brucejcooper/light_controller/kicad/programmer/programmer.kicad_pcb

## KiCad design cores/cps3/sch/buffer_line_driver.kicad_sch

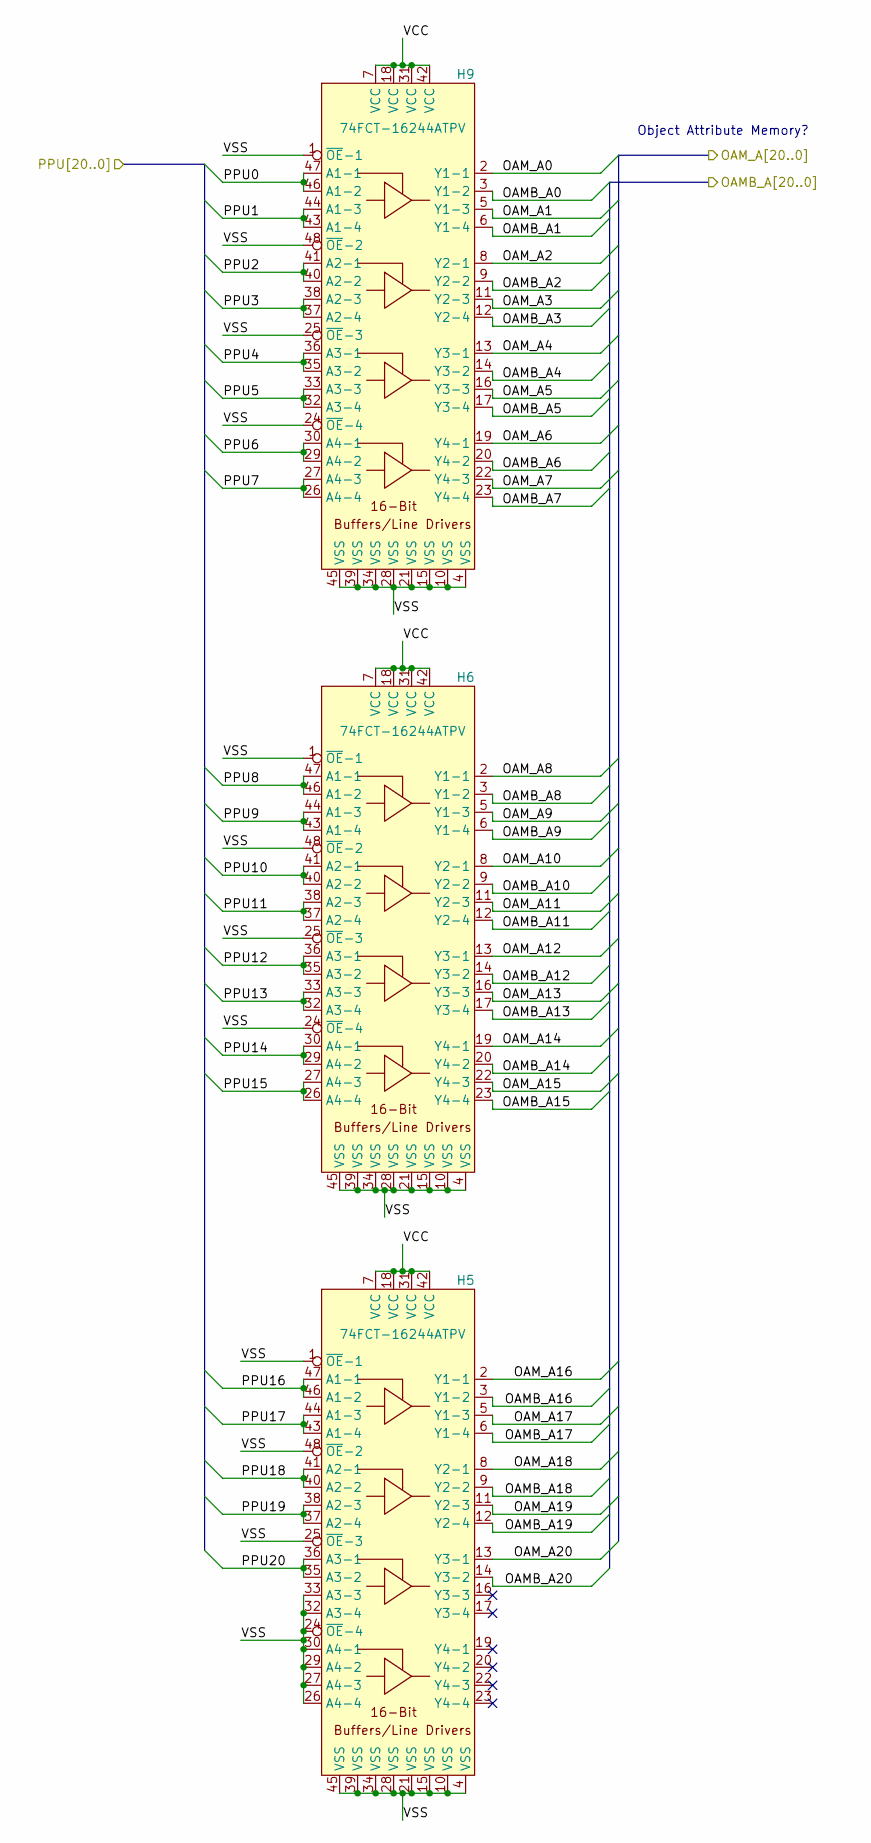
[picture p15: schematic buffer_line_driver.kicad_sch]

Parts:
H5, H6, H9: 74FCT-16244ATPV

Connections:
OAMB_A0: H9.3 (Y1-2)
OAMB_A1: H9.6 (Y1-4)
OAMB_A2: H9.9 (Y2-2)
OAMB_A3: H9.12 (Y2-4)
OAMB_A4: H9.14 (Y3-2)
OAMB_A5: H9.17 (Y3-4)
OAMB_A6: H9.20 (Y4-2)
OAMB_A7: H9.23 (Y4-4)
OAMB_A8: H6.3 (Y1-2)
OAMB_A9: H6.6 (Y1-4)
OAMB_A10: H6.9 (Y2-2)
OAMB_A11: H6.12 (Y2-4)
OAMB_A12: H6.14 (Y3-2)
OAMB_A13: H6.17 (Y3-4)
OAMB_A14: H6.20 (Y4-2)
OAMB_A15: H6.23 (Y4-4)
OAMB_A16: H5.3 (Y1-2)
OAMB_A17: H5.6 (Y1-4)
OAMB_A18: H5.9 (Y2-2)
OAMB_A19: H5.12 (Y2-4)
OAMB_A20: H5.14 (Y3-2)
OAM_A0: H9.2 (Y1-1)
OAM_A1: H9.5 (Y1-3)
OAM_A2: H9.8 (Y2-1)
OAM_A3: H9.11 (Y2-3)
OAM_A4: H9.13 (Y3-1)
OAM_A5: H9.16 (Y3-3)
OAM_A6: H9.19 (Y4-1)
OAM_A7: H9.22 (Y4-3)
OAM_A8: H6.2 (Y1-1)
OAM_A9: H6.5 (Y1-3)
OAM_A10: H6.8 (Y2-1)
OAM_A11: H6.11 (Y2-3)
OAM_A12: H6.13 (Y3-1)
OAM_A13: H6.16 (Y3-3)
OAM_A14: H6.19 (Y4-1)
OAM_A15: H6.22 (Y4-3)
OAM_A16: H5.2 (Y1-1)
OAM_A17: H5.5 (Y1-3)
OAM_A18: H5.8 (Y2-1)
OAM_A19: H5.11 (Y2-3)
OAM_A20: H5.13 (Y3-1)
PPU0: H9.46 (A1-2), H9.47 (A1-1)
PPU1: H9.43 (A1-4), H9.44 (A1-3)
PPU2: H9.40 (A2-2), H9.41 (A2-1)
PPU3: H9.37 (A2-4), H9.38 (A2-3)
PPU4: H9.35 (A3-2), H9.36 (A3-1)
PPU5: H9.32 (A3-4), H9.33 (A3-3)
PPU6: H9.29 (A4-2), H9.30 (A4-1)
PPU7: H9.26 (A4-4), H9.27 (A4-3)
PPU8: H6.46 (A1-2), H6.47 (A1-1)
PPU9: H6.43 (A1-4), H6.44 (A1-3)
PPU10: H6.40 (A2-2), H6.41 (A2-1)
PPU11: H6.37 (A2-4), H6.38 (A2-3)
PPU12: H6.35 (A3-2), H6.36 (A3-1)
PPU13: H6.32 (A3-4), H6.33 (A3-3)
PPU14: H6.29 (A4-2), H6.30 (A4-1)
PPU15: H6.26 (A4-4), H6.27 (A4-3)
PPU16: H5.46 (A1-2), H5.47 (A1-1)
PPU17: H5.43 (A1-4), H5.44 (A1-3)
PPU18: H5.40 (A2-2), H5.41 (A2-1)
PPU19: H5.37 (A2-4), H5.38 (A2-3)
PPU20: H5.35 (A3-2), H5.36 (A3-1)
VCC: H5.7 (VCC), H5.18 (VCC), H5.31 (VCC), H5.42 (VCC), H6.7 (VCC), H6.18 (VCC), H6.31 (VCC), H6.42 (VCC), H9.7 (VCC), H9.18 (VCC), H9.31 (VCC), H9.42 (VCC)
VSS: H5.1 (~OE-1), H5.4 (VSS), H5.10 (VSS), H5.15 (VSS), H5.21 (VSS), H5.24 (~OE-4), H5.25 (~OE-3), H5.26 (A4-4), H5.27 (A4-3), H5.28 (VSS), H5.29 (A4-2), H5.30 (A4-1), H5.32 (A3-4), H5.33 (A3-3), H5.34 (VSS), H5.39 (VSS), H5.45 (VSS), H5.48 (~OE-2), H6.1 (~OE-1), H6.4 (VSS), H6.10 (VSS), H6.15 (VSS), H6.21 (VSS), H6.24 (~OE-4), H6.25 (~OE-3), H6.28 (VSS), H6.34 (VSS), H6.39 (VSS), H6.45 (VSS), H6.48 (~OE-2), H9.1 (~OE-1), H9.4 (VSS), H9.10 (VSS), H9.15 (VSS), H9.21 (VSS), H9.24 (~OE-4), H9.25 (~OE-3), H9.28 (VSS), H9.34 (VSS), H9.39 (VSS), H9.45 (VSS), H9.48 (~OE-2)

Notes on the sheet:
Object Attribute Memory?
