brucejcooper/light_controller/kicad/programmer/programmer.kicad_pcb

## KiCad design cores/cps3/sch/cassette.kicad_sch

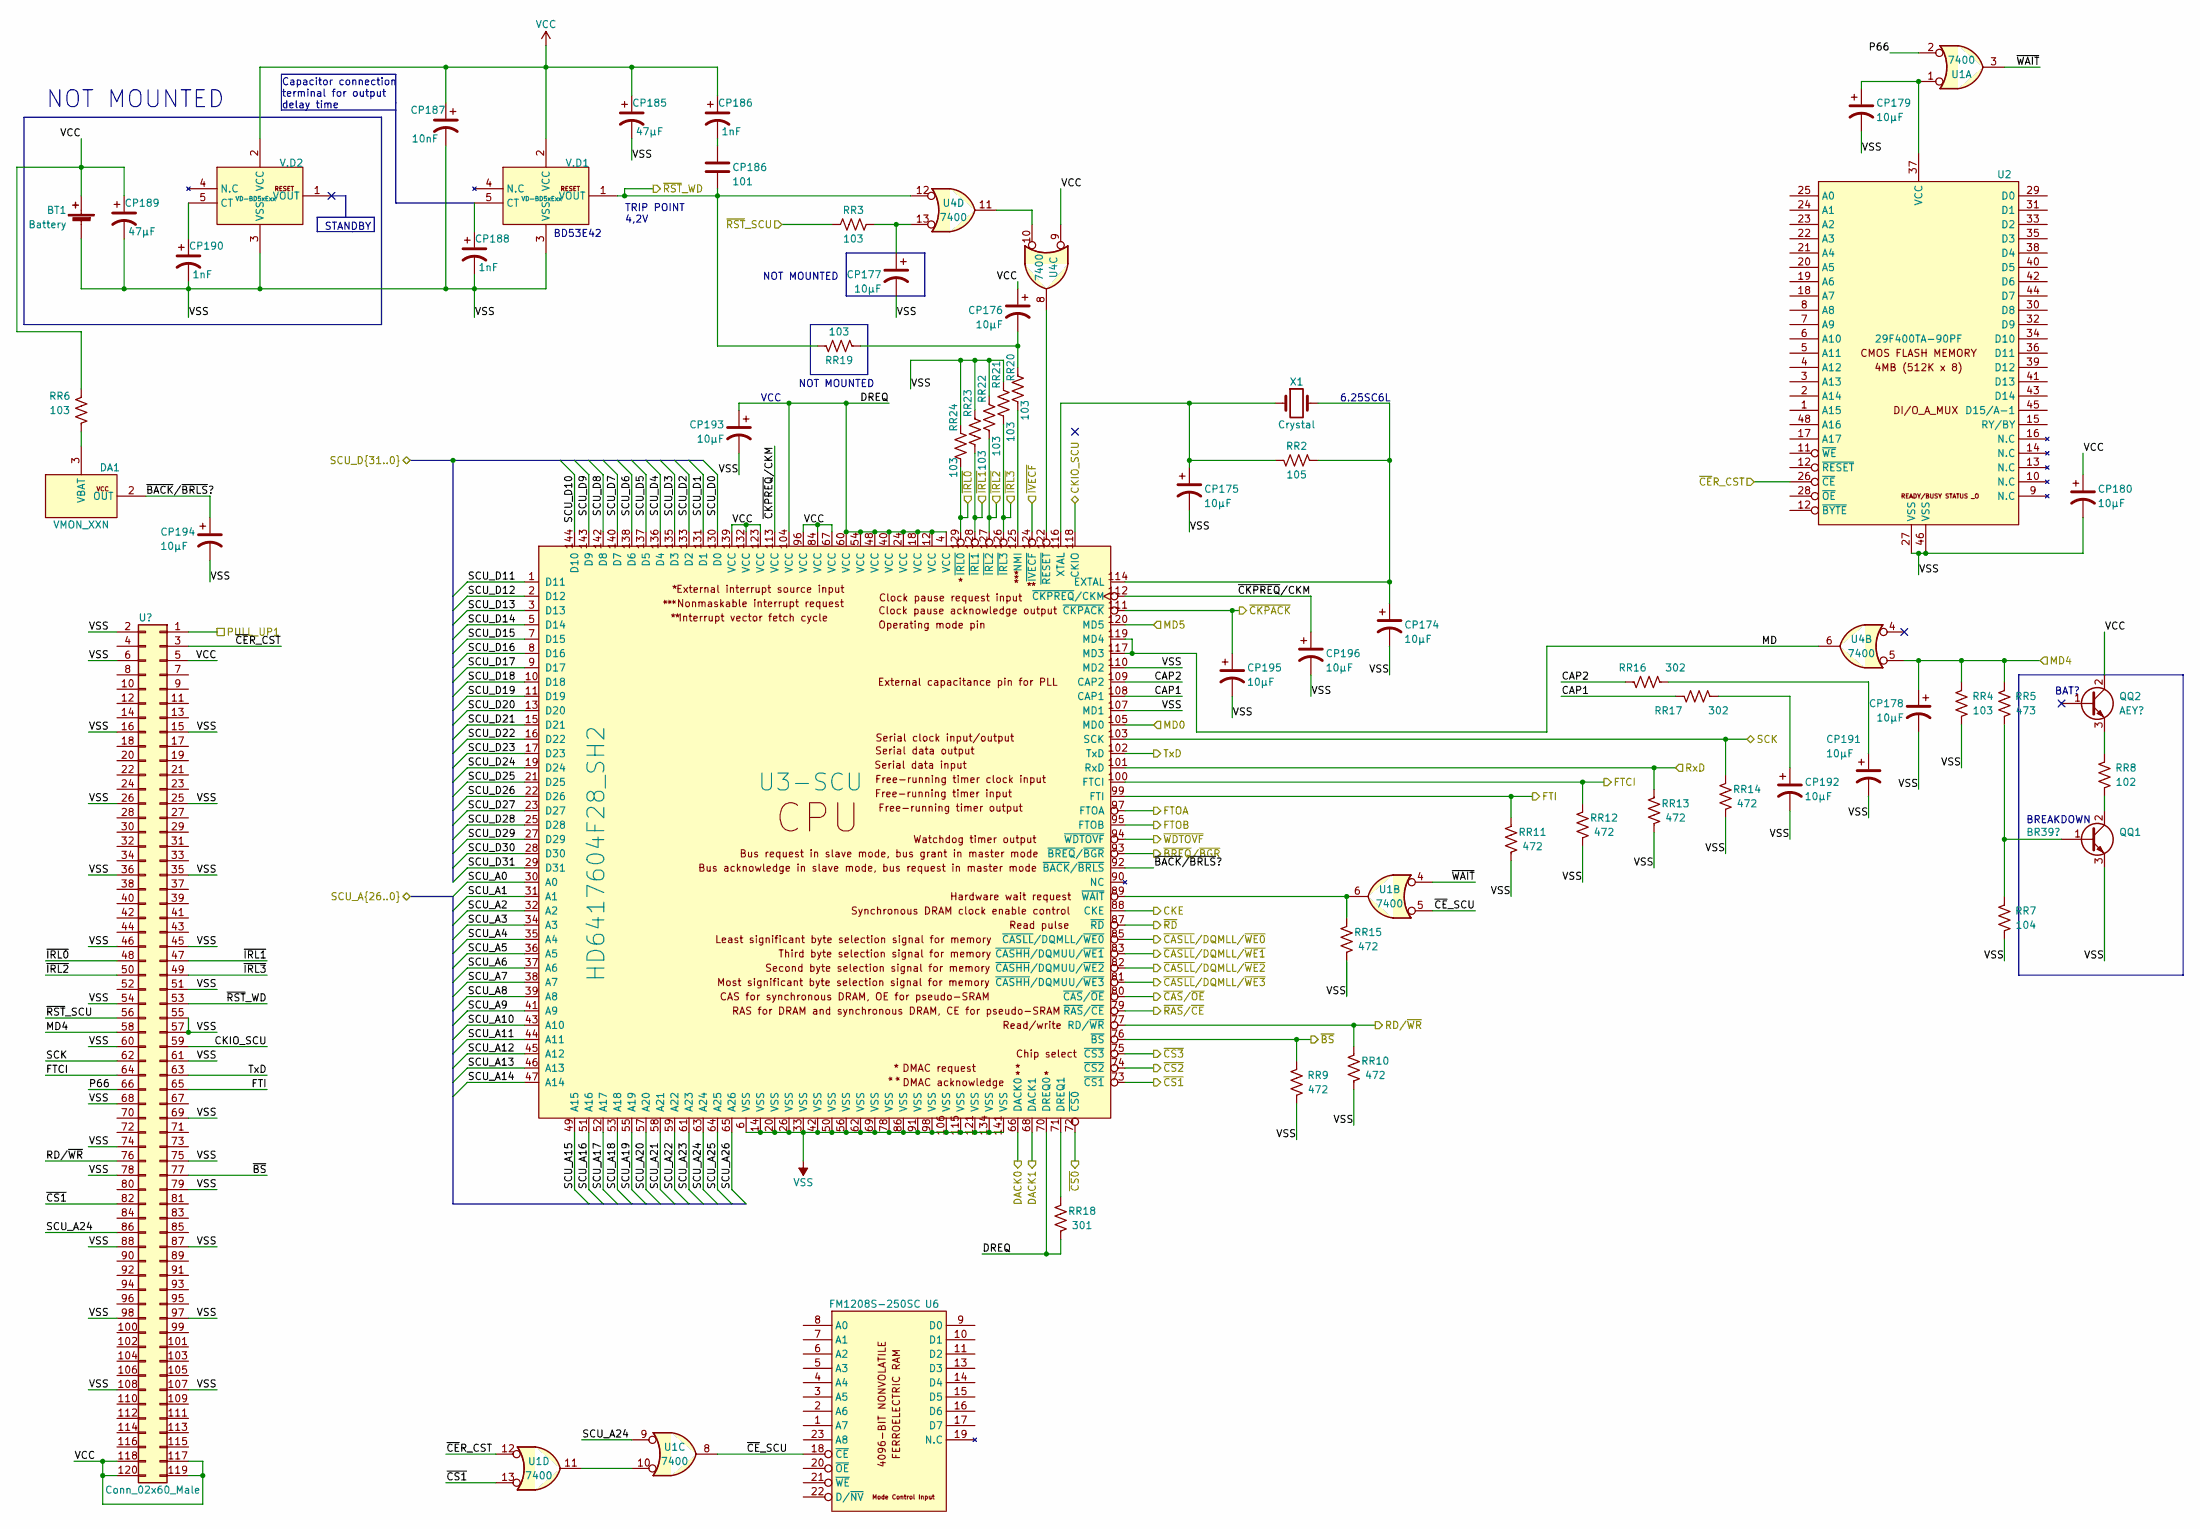
[picture p17: schematic cassette.kicad_sch]

Parts:
BT1: Battery
CP174, CP175, CP176, CP177, CP178, CP179, CP180, CP191, CP192, CP193, CP194, CP195, CP196: 10μF
CP185, CP189: 47μF
CP186: 101
CP187: 10nF
CP188, CP190: 1nF
DA1: VMON_XXN
QQ1: BR39?
QQ2: AEY?
RR2: 105
RR3, RR4, RR6, RR19, RR20, RR21, RR22, RR23, RR24: 103
RR5: 473
RR7: 104
RR8: 102
RR9, RR10, RR11, RR12, RR13, RR14, RR15: 472
RR16, RR17: 302
RR18: 301
U1, U4: 7400
U2: 29F400TA-90PF
U3-SCU: HD6417604F28_SH2
U6: FM1208S-250SC
V.D1, V.D2: VD-BD5xExx
X1: Crystal

Connections:
CAP1: RR17.2, U3-SCU.108 (CAP1)
CAP2: RR16.2, U3-SCU.109 (CAP2)
CKE: U3-SCU.88 (CKE)
CKIO_SCU: U3-SCU.118 (CKIO)
DACK0: U3-SCU.66 (DACK0)
DACK1: U3-SCU.68 (DACK1)
DREQ: CP193.1, RR18.2, U3-SCU.4 (VCC), U3-SCU.12 (VCC), U3-SCU.18 (VCC), U3-SCU.24 (VCC), U3-SCU.40 (VCC), U3-SCU.48 (VCC), U3-SCU.54 (VCC), U3-SCU.60 (VCC), U3-SCU.70 (DREQ0), U3-SCU.104 (VCC)
FTCI: RR12.2, U3-SCU.100 (FTCI)
FTI: RR11.2, U3-SCU.99 (FTI)
FTOA: U3-SCU.97 (FTOA)
FTOB: U3-SCU.95 (FTOB)
MD: U3-SCU.117 (MD3), U3-SCU.119 (MD4), U4.6
MD0: U3-SCU.105 (MD0)
MD4: CP178.1, RR4.2, RR5.2, U4.5
MD5: U3-SCU.120 (MD5)
unnamed: CP174.1, RR2.2, U3-SCU.114 (EXTAL), X1.2
unnamed: CP175.1, RR2.1, U3-SCU.116 (XTAL), X1.1
unnamed: CP176.2, RR19.2, RR20.2
unnamed: CP177.1, RR3.2, U4.13
unnamed: CP179.1, U1.1, U2.37 (VCC)
unnamed: CP185.1, CP186.1, CP187.1, V.D1.2 (VCC), V.D2.2 (VCC)
unnamed: CP188.1, V.D1.5 (CT)
unnamed: CP190.1, V.D2.5 (CT)
unnamed: CP191.1, RR16.1
unnamed: CP192.1, RR17.1
unnamed: DA1.3 (VBAT), RR6.1
unnamed: QQ1.1 (B), RR5.1, RR7.2
unnamed: QQ1.2 (C), RR8.1
unnamed: QQ2.3 (E), RR8.2
unnamed: RR15.2, U1.6, U3-SCU.89 (~WAIT)
unnamed: RR18.1, U3-SCU.71 (DREQ1)
unnamed: RR20.1, U3-SCU.125 (NMI)
unnamed: U1.10, U1.11
unnamed: U3-SCU.6 (VSS), U3-SCU.14 (VSS), U3-SCU.20 (VSS), U3-SCU.26 (VSS), U3-SCU.33 (VSS), U3-SCU.42 (VSS), U3-SCU.50 (VSS), U3-SCU.56 (VSS), U3-SCU.62 (VSS), U3-SCU.69 (VSS), U3-SCU.78 (VSS), U3-SCU.86 (VSS), U3-SCU.91 (VSS), U3-SCU.98 (VSS), U3-SCU.106 (VSS), U3-SCU.115 (VSS), U3-SCU.121 (VSS), U3-SCU.134 (VSS), U3-SCU.141 (VSS)
unnamed: U3-SCU.122 (~RESET), U4.8
unnamed: U4.10, U4.11
P66: U1.2
RD/~WR: RR10.2, U3-SCU.77 (RD/~WR)
RxD: RR13.2, U3-SCU.101 (RxD)
SCK: RR14.2, U3-SCU.103 (SCK)
SCU_A0: U3-SCU.30 (A0)
SCU_A1: U3-SCU.31 (A1)
SCU_A2: U3-SCU.32 (A2)
SCU_A3: U3-SCU.34 (A3)
SCU_A4: U3-SCU.35 (A4)
SCU_A5: U3-SCU.36 (A5)
SCU_A6: U3-SCU.37 (A6)
SCU_A7: U3-SCU.38 (A7)
SCU_A8: U3-SCU.39 (A8)
SCU_A9: U3-SCU.41 (A9)
SCU_A10: U3-SCU.43 (A10)
SCU_A11: U3-SCU.44 (A11)
SCU_A12: U3-SCU.45 (A12)
SCU_A13: U3-SCU.46 (A13)
SCU_A14: U3-SCU.47 (A14)
SCU_A15: U3-SCU.49 (A15)
SCU_A16: U3-SCU.51 (A16)
SCU_A17: U3-SCU.52 (A17)
SCU_A18: U3-SCU.53 (A18)
SCU_A19: U3-SCU.55 (A19)
SCU_A20: U3-SCU.57 (A20)
SCU_A21: U3-SCU.58 (A21)
SCU_A22: U3-SCU.59 (A22)
SCU_A23: U3-SCU.61 (A23)
SCU_A24: U1.9, U3-SCU.63 (A24)
SCU_A25: U3-SCU.64 (A25)
SCU_A26: U3-SCU.65 (A26)
SCU_D0: U3-SCU.130 (D0)
SCU_D1: U3-SCU.131 (D1)
SCU_D2: U3-SCU.133 (D2)
SCU_D3: U3-SCU.135 (D3)
SCU_D4: U3-SCU.136 (D4)
SCU_D5: U3-SCU.137 (D5)
SCU_D6: U3-SCU.138 (D6)
SCU_D7: U3-SCU.140 (D7)
SCU_D8: U3-SCU.142 (D8)
SCU_D9: U3-SCU.143 (D9)
SCU_D10: U3-SCU.144 (D10)
SCU_D11: U3-SCU.1 (D11)
SCU_D12: U3-SCU.2 (D12)
SCU_D13: U3-SCU.3 (D13)
SCU_D14: U3-SCU.5 (D14)
SCU_D15: U3-SCU.7 (D15)
SCU_D16: U3-SCU.8 (D16)
SCU_D17: U3-SCU.9 (D17)
SCU_D18: U3-SCU.10 (D18)
SCU_D19: U3-SCU.11 (D19)
SCU_D20: U3-SCU.13 (D20)
SCU_D21: U3-SCU.15 (D21)
SCU_D22: U3-SCU.16 (D22)
SCU_D23: U3-SCU.17 (D23)
SCU_D24: U3-SCU.19 (D24)
SCU_D25: U3-SCU.21 (D25)
SCU_D26: U3-SCU.22 (D26)
SCU_D27: U3-SCU.23 (D27)
SCU_D28: U3-SCU.25 (D28)
SCU_D29: U3-SCU.27 (D29)
SCU_D30: U3-SCU.28 (D30)
SCU_D31: U3-SCU.29 (D31)
TxD: U3-SCU.102 (TxD)
VCC: BT1.1 (+), CP176.1, CP180.1, CP189.1, QQ2.2 (C), RR6.2, U3-SCU.67 (VCC), U3-SCU.84 (VCC), U3-SCU.96 (VCC), U3-SCU.123 (VCC), U3-SCU.132 (VCC), U3-SCU.139 (VCC), U4.9
VSS: BT1.2 (-), CP174.2, CP175.2, CP177.2, CP178.2, CP179.2, CP180.2, CP185.2, CP187.2, CP188.2, CP189.2, CP190.2, CP191.2, CP192.2, CP193.2, CP194.2, CP195.2, CP196.2, QQ1.3 (E), RR4.1, RR7.1, RR9.1, RR10.1, RR11.1, RR12.1, RR13.1, RR14.1, RR15.1, RR21.2, RR22.2, RR23.2, RR24.2, U2.27 (VSS), U2.46 (VSS), U3-SCU.107 (MD1), U3-SCU.110 (MD2), V.D1.3 (VSS), V.D2.3 (VSS)
~BACK/~BRLS?: CP194.1, DA1.2 (OUT), U3-SCU.92 (~BACK/~BRLS)
~BREQ/~BGR: U3-SCU.93 (~BREQ/~BGR)
~BS: RR9.2, U3-SCU.76 (~BS)
~CASLL/DQMLL/~WE0: U3-SCU.85 (~CASLL/DQMLL/~WE0)
~CASLL/DQMLL/~WE1: U3-SCU.83 (~CASHH/DQMUU/~WE1)
~CASLL/DQMLL/~WE2: U3-SCU.82 (~CASHH/DQMUU/~WE2)
~CASLL/DQMLL/~WE3: U3-SCU.81 (~CASHH/DQMUU/~WE3)
~CAS/~OE: U3-SCU.80 (~CAS/~OE)
~CER_CST: U1.12, U2.26 (~CE)
~CE_SCU: U1.5, U1.8, U6.18 (~CE)
~CKPACK: CP195.1, U3-SCU.111 (~CKPACK)
~CKPREQ/CKM: CP196.1, U3-SCU.112 (~CKPREQ/CKM), U3-SCU.113 (VCC)
~CS0: U3-SCU.72 (~CS0)
~CS1: U1.13, U3-SCU.73 (~CS1)
~CS2: U3-SCU.74 (~CS2)
~CS3: U3-SCU.75 (~CS3)
~IRL0: RR24.1, U3-SCU.129 (~IRL0)
~IRL1: RR23.1, U3-SCU.128 (~IRL1)
~IRL2: RR22.1, U3-SCU.127 (~IRL2)
~IRL3: RR21.1, U3-SCU.126 (~IRL3)
~IVECF: U3-SCU.124 (~IVECF)
~RAS/~CE: U3-SCU.79 (~RAS/~CE)
~RD: U3-SCU.87 (~RD)
~RST_SCU: RR3.1
~RST_WD: CP186.1, RR19.1, U4.12, V.D1.1 (VOUT)
~WAIT: U1.3, U1.4
~WDTOVF: U3-SCU.94 (~WDTOVF)

Notes on the sheet:
BREAKDOWN
Capacitor connection terminal for output delay time
VCC
BAT?
6.25SC6L
BD53E42
NOT MOUNTED
TRIP POINT 4,2V
STANDBY
