brucejcooper/light_controller/kicad/programmer/programmer.kicad_pcb

## KiCad design cores/cps3/sch/memories_fb.kicad_sch

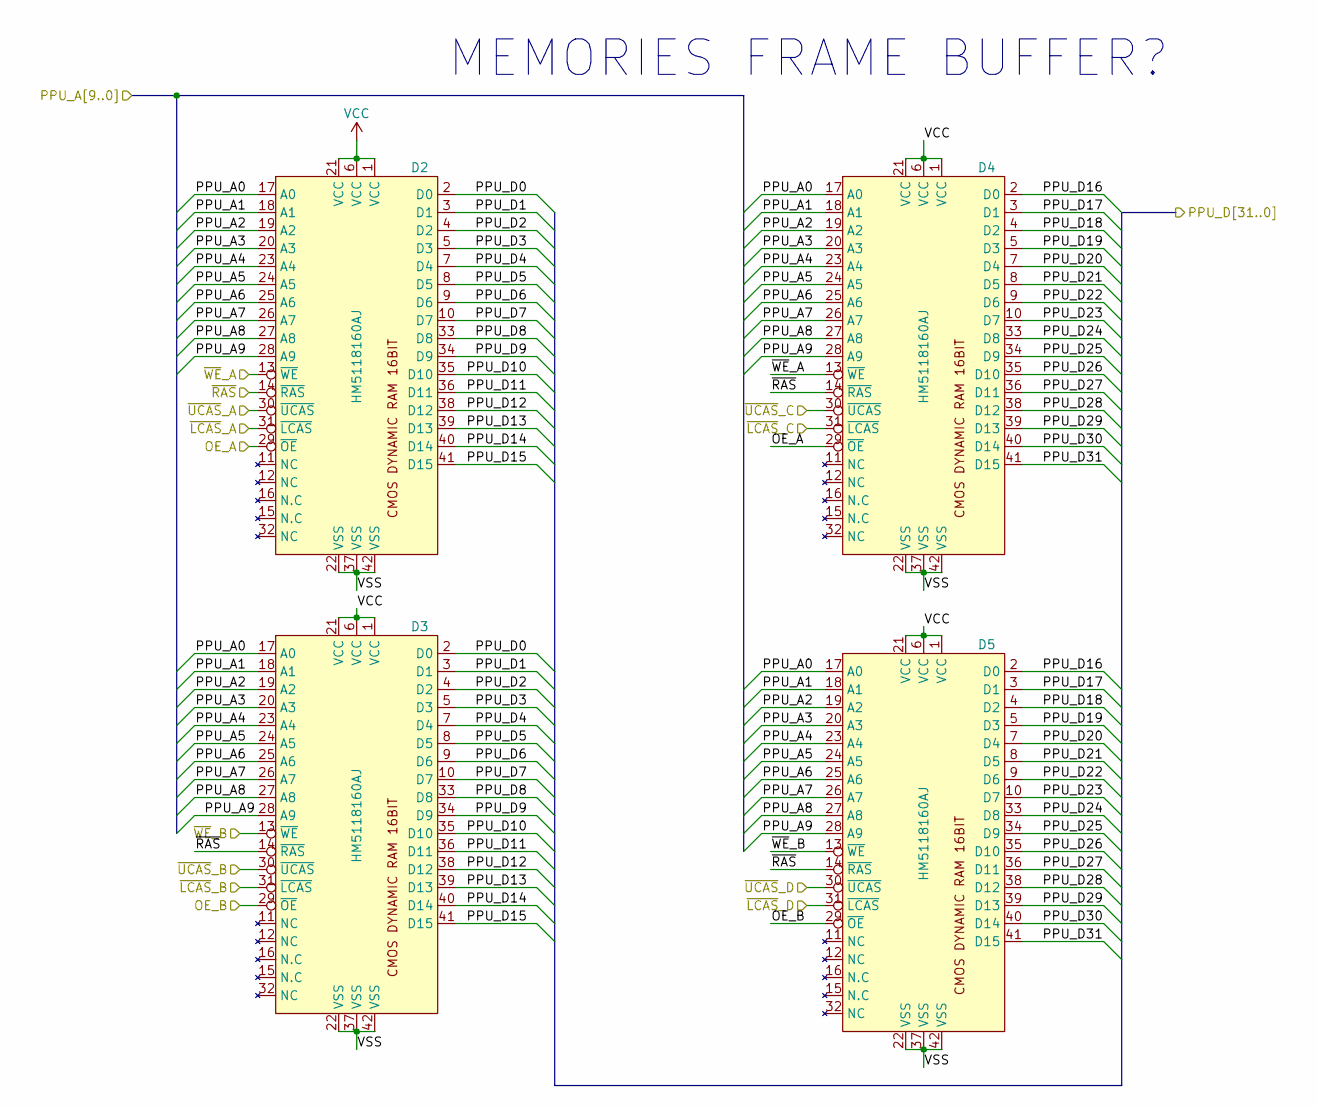
[picture p21: schematic memories_fb.kicad_sch]

Parts:
D2, D3, D4, D5: HM5118160AJ

Connections:
unnamed: D2.1 (VCC), D2.6 (VCC), D2.21 (VCC)
OE_A: D2.29 (~OE), D4.29 (~OE)
OE_B: D3.29 (~OE), D5.29 (~OE)
PPU_A0: D2.17 (A0), D3.17 (A0), D4.17 (A0), D5.17 (A0)
PPU_A1: D2.18 (A1), D3.18 (A1), D4.18 (A1), D5.18 (A1)
PPU_A2: D2.19 (A2), D3.19 (A2), D4.19 (A2), D5.19 (A2)
PPU_A3: D2.20 (A3), D3.20 (A3), D4.20 (A3), D5.20 (A3)
PPU_A4: D2.23 (A4), D3.23 (A4), D4.23 (A4), D5.23 (A4)
PPU_A5: D2.24 (A5), D3.24 (A5), D4.24 (A5), D5.24 (A5)
PPU_A6: D2.25 (A6), D3.25 (A6), D4.25 (A6), D5.25 (A6)
PPU_A7: D2.26 (A7), D3.26 (A7), D4.26 (A7), D5.26 (A7)
PPU_A8: D2.27 (A8), D3.27 (A8), D4.27 (A8), D5.27 (A8)
PPU_A9: D2.28 (A9), D3.28 (A9), D4.28 (A9), D5.28 (A9)
PPU_D0: D2.2 (D0), D3.2 (D0)
PPU_D1: D2.3 (D1), D3.3 (D1)
PPU_D2: D2.4 (D2), D3.4 (D2)
PPU_D3: D2.5 (D3), D3.5 (D3)
PPU_D4: D2.7 (D4), D3.7 (D4)
PPU_D5: D2.8 (D5), D3.8 (D5)
PPU_D6: D2.9 (D6), D3.9 (D6)
PPU_D7: D2.10 (D7), D3.10 (D7)
PPU_D8: D2.33 (D8), D3.33 (D8)
PPU_D9: D2.34 (D9), D3.34 (D9)
PPU_D10: D2.35 (D10), D3.35 (D10)
PPU_D11: D2.36 (D11), D3.36 (D11)
PPU_D12: D2.38 (D12), D3.38 (D12)
PPU_D13: D2.39 (D13), D3.39 (D13)
PPU_D14: D2.40 (D14), D3.40 (D14)
PPU_D15: D2.41 (D15), D3.41 (D15)
PPU_D16: D4.2 (D0), D5.2 (D0)
PPU_D17: D4.3 (D1), D5.3 (D1)
PPU_D18: D4.4 (D2), D5.4 (D2)
PPU_D19: D4.5 (D3), D5.5 (D3)
PPU_D20: D4.7 (D4), D5.7 (D4)
PPU_D21: D4.8 (D5), D5.8 (D5)
PPU_D22: D4.9 (D6), D5.9 (D6)
PPU_D23: D4.10 (D7), D5.10 (D7)
PPU_D24: D4.33 (D8), D5.33 (D8)
PPU_D25: D4.34 (D9), D5.34 (D9)
PPU_D26: D4.35 (D10), D5.35 (D10)
PPU_D27: D4.36 (D11), D5.36 (D11)
PPU_D28: D4.38 (D12), D5.38 (D12)
PPU_D29: D4.39 (D13), D5.39 (D13)
PPU_D30: D4.40 (D14), D5.40 (D14)
PPU_D31: D4.41 (D15), D5.41 (D15)
VCC: D3.1 (VCC), D3.6 (VCC), D3.21 (VCC), D4.1 (VCC), D4.6 (VCC), D4.21 (VCC), D5.1 (VCC), D5.6 (VCC), D5.21 (VCC)
VSS: D2.22 (VSS), D2.37 (VSS), D2.42 (VSS), D3.22 (VSS), D3.37 (VSS), D3.42 (VSS), D4.22 (VSS), D4.37 (VSS), D4.42 (VSS), D5.22 (VSS), D5.37 (VSS), D5.42 (VSS)
~LCAS_A: D2.31 (~LCAS)
~LCAS_B: D3.31 (~LCAS)
~LCAS_C: D4.31 (~LCAS)
~LCAS_D: D5.31 (~LCAS)
~RAS: D2.14 (~RAS), D3.14 (~RAS), D4.14 (~RAS), D5.14 (~RAS)
~UCAS_A: D2.30 (~UCAS)
~UCAS_B: D3.30 (~UCAS)
~UCAS_C: D4.30 (~UCAS)
~UCAS_D: D5.30 (~UCAS)
~WE_A: D2.13 (~WE), D4.13 (~WE)
~WE_B: D3.13 (~WE), D5.13 (~WE)

Notes on the sheet:
MEMORIES FRAME BUFFER?
