brucejcooper/light_controller/kicad/programmer/programmer.kicad_pcb

## KiCad design cores/cps3/sch/memories_scu.kicad_sch

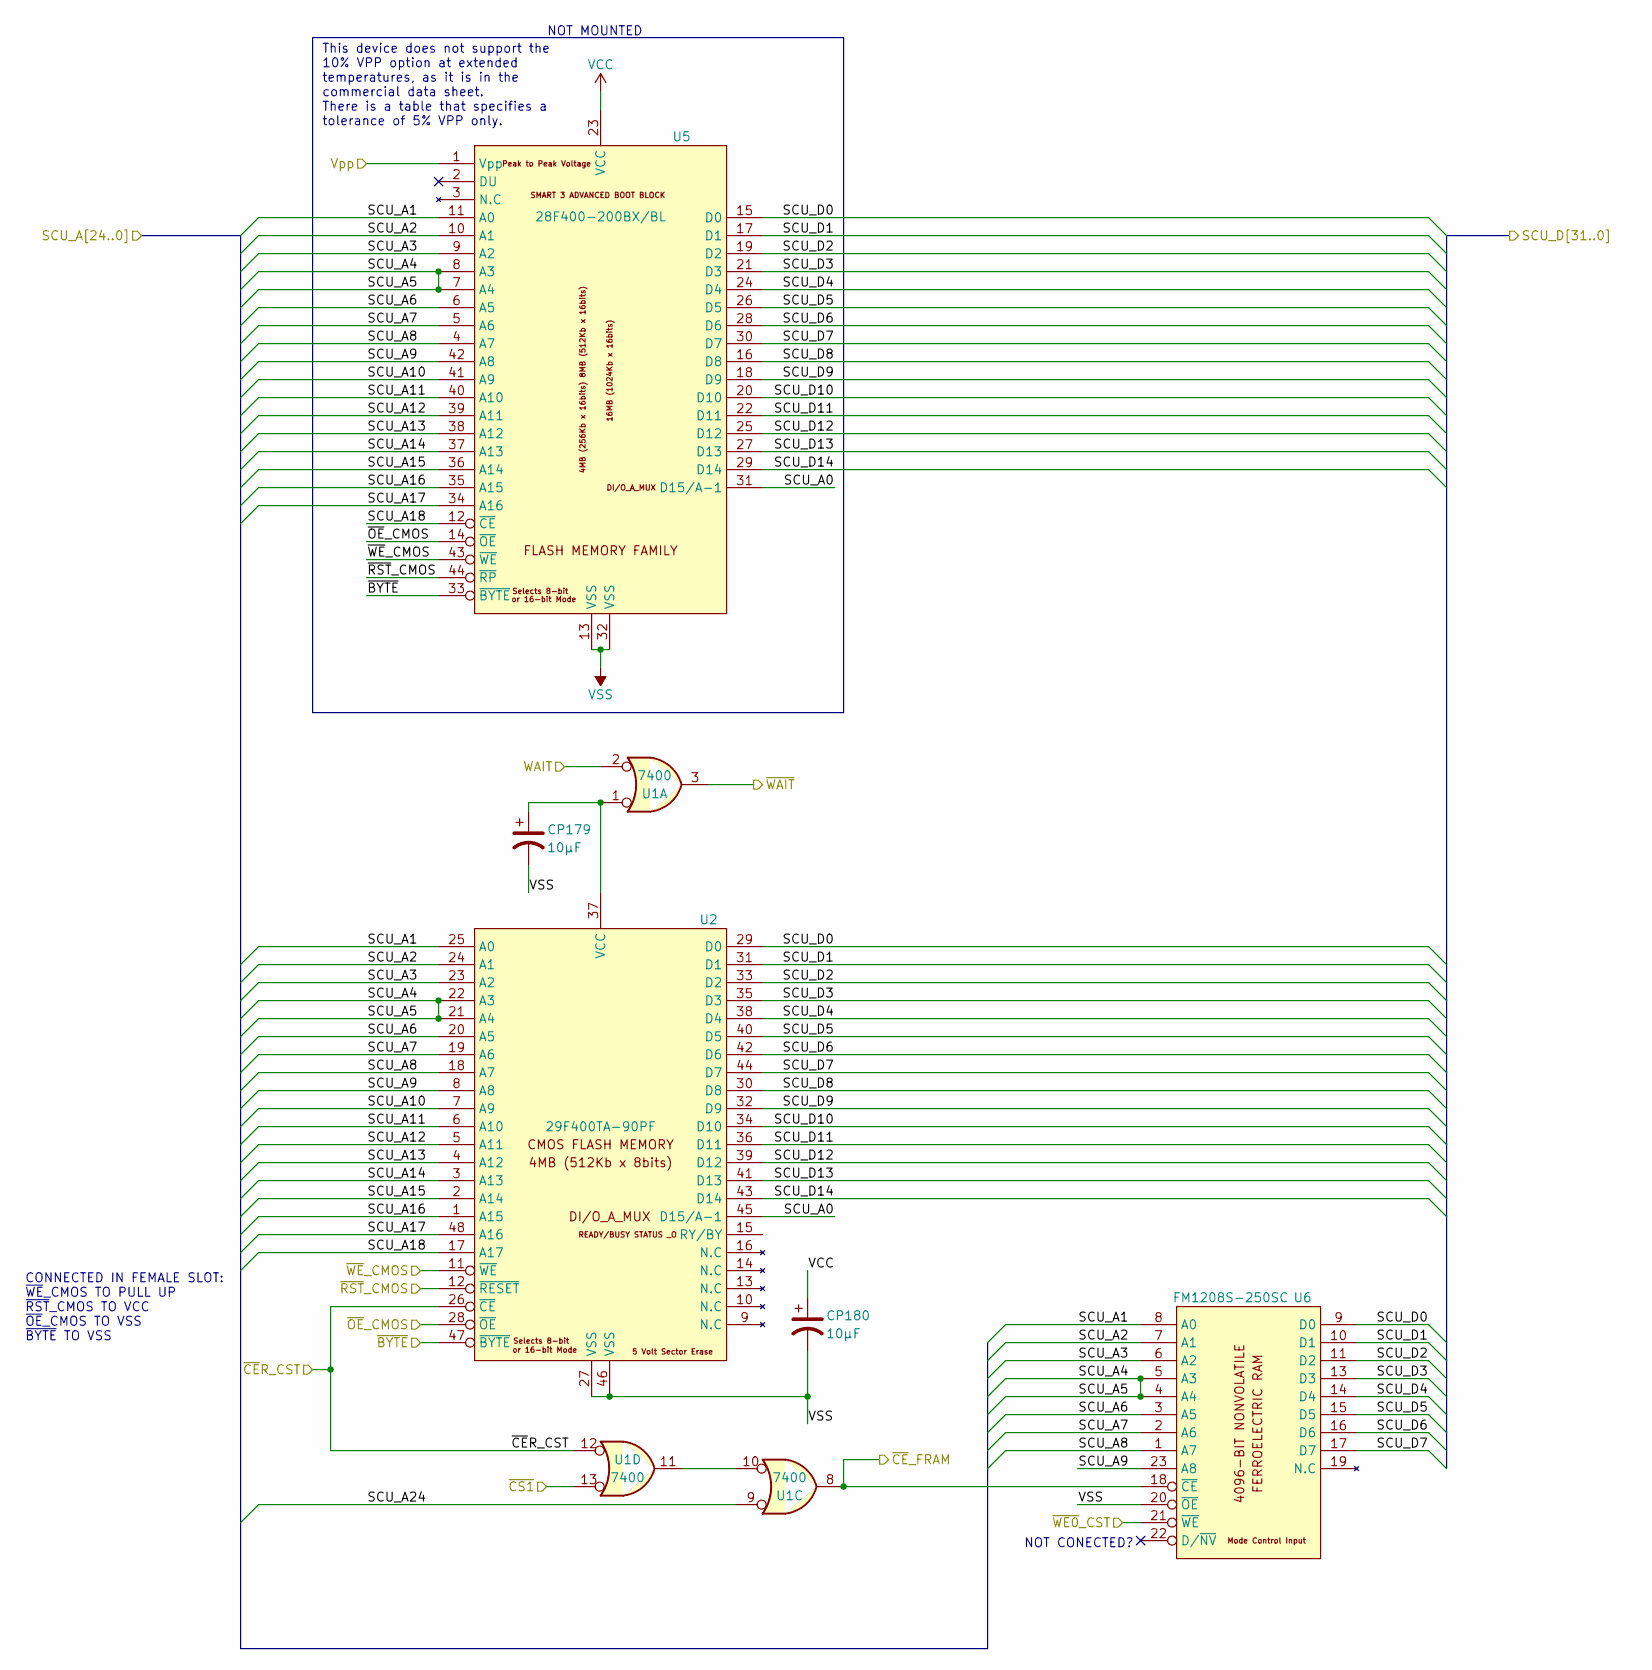
[picture p22: schematic memories_scu.kicad_sch]

Parts:
CP179, CP180: 10μF
U1: 7400
U2: 29F400TA-90PF
U5: 28F400-200BX/BL
U6: FM1208S-250SC

Connections:
unnamed: CP179.1, U1.1, U2.37 (VCC)
unnamed: U1.10, U1.11
unnamed: U5.13 (VSS), U5.32 (VSS)
SCU_A0: U2.45 (D15/A-1), U5.31 (D15/A-1)
SCU_A1: U2.25 (A0), U5.11 (A0), U6.8 (A0)
SCU_A2: U2.24 (A1), U5.10 (A1), U6.7 (A1)
SCU_A3: U2.23 (A2), U5.9 (A2), U6.6 (A2)
SCU_A4: U2.21 (A4), U2.22 (A3), U5.7 (A4), U5.8 (A3), U6.4 (A4), U6.5 (A3)
SCU_A6: U2.20 (A5), U5.6 (A5), U6.3 (A5)
SCU_A7: U2.19 (A6), U5.5 (A6), U6.2 (A6)
SCU_A8: U2.18 (A7), U5.4 (A7), U6.1 (A7)
SCU_A9: U2.8 (A8), U5.42 (A8), U6.23 (A8)
SCU_A10: U2.7 (A9), U5.41 (A9)
SCU_A11: U2.6 (A10), U5.40 (A10)
SCU_A12: U2.5 (A11), U5.39 (A11)
SCU_A13: U2.4 (A12), U5.38 (A12)
SCU_A14: U2.3 (A13), U5.37 (A13)
SCU_A15: U2.2 (A14), U5.36 (A14)
SCU_A16: U2.1 (A15), U5.35 (A15)
SCU_A17: U2.48 (A16), U5.34 (A16)
SCU_A18: U2.17 (A17), U5.12 (~CE)
SCU_A24: U1.9
SCU_D0: U2.29 (D0), U5.15 (D0), U6.9 (D0)
SCU_D1: U2.31 (D1), U5.17 (D1), U6.10 (D1)
SCU_D2: U2.33 (D2), U5.19 (D2), U6.11 (D2)
SCU_D3: U2.35 (D3), U5.21 (D3), U6.13 (D3)
SCU_D4: U2.38 (D4), U5.24 (D4), U6.14 (D4)
SCU_D5: U2.40 (D5), U5.26 (D5), U6.15 (D5)
SCU_D6: U2.42 (D6), U5.28 (D6), U6.16 (D6)
SCU_D7: U2.44 (D7), U5.30 (D7), U6.17 (D7)
SCU_D8: U2.30 (D8), U5.16 (D8)
SCU_D9: U2.32 (D9), U5.18 (D9)
SCU_D10: U2.34 (D10), U5.20 (D10)
SCU_D11: U2.36 (D11), U5.22 (D11)
SCU_D12: U2.39 (D12), U5.25 (D12)
SCU_D13: U2.41 (D13), U5.27 (D13)
SCU_D14: U2.43 (D14), U5.29 (D14)
VCC: CP180.1
VSS: CP179.2, CP180.2, U2.27 (VSS), U2.46 (VSS), U6.20 (~OE)
Vpp: U5.1 (Vpp)
WAIT: U1.2
~BYTE: U2.47 (~BYTE), U5.33 (~BYTE)
~CER_CST: U1.12, U2.26 (~CE)
~CE_FRAM: U1.8, U6.18 (~CE)
~CS1: U1.13
~OE_CMOS: U2.28 (~OE), U5.14 (~OE)
~RST_CMOS: U2.12 (~RESET), U5.44 (~RP)
~WAIT: U1.3
~WE0_CST: U6.21 (~WE)
~WE_CMOS: U2.11 (~WE), U5.43 (~WE)

Notes on the sheet:
NOT CONECTED?
NOT MOUNTED
CONNECTED IN FEMALE SLOT: ~{WE}_CMOS TO PULL UP ~{RST}_CMOS TO VCC ~{OE}_CMOS TO VSS ~{BYTE} TO VSS
This device does not support the 10% VPP option at extended temperatures, as it is in the commercial data sheet. There is a table that specifies a tolerance of 5% VPP only.
