brucejcooper/light_controller/kicad/programmer/programmer.kicad_pcb

## KiCad design cores/cps3/sch/simm3.kicad_sch

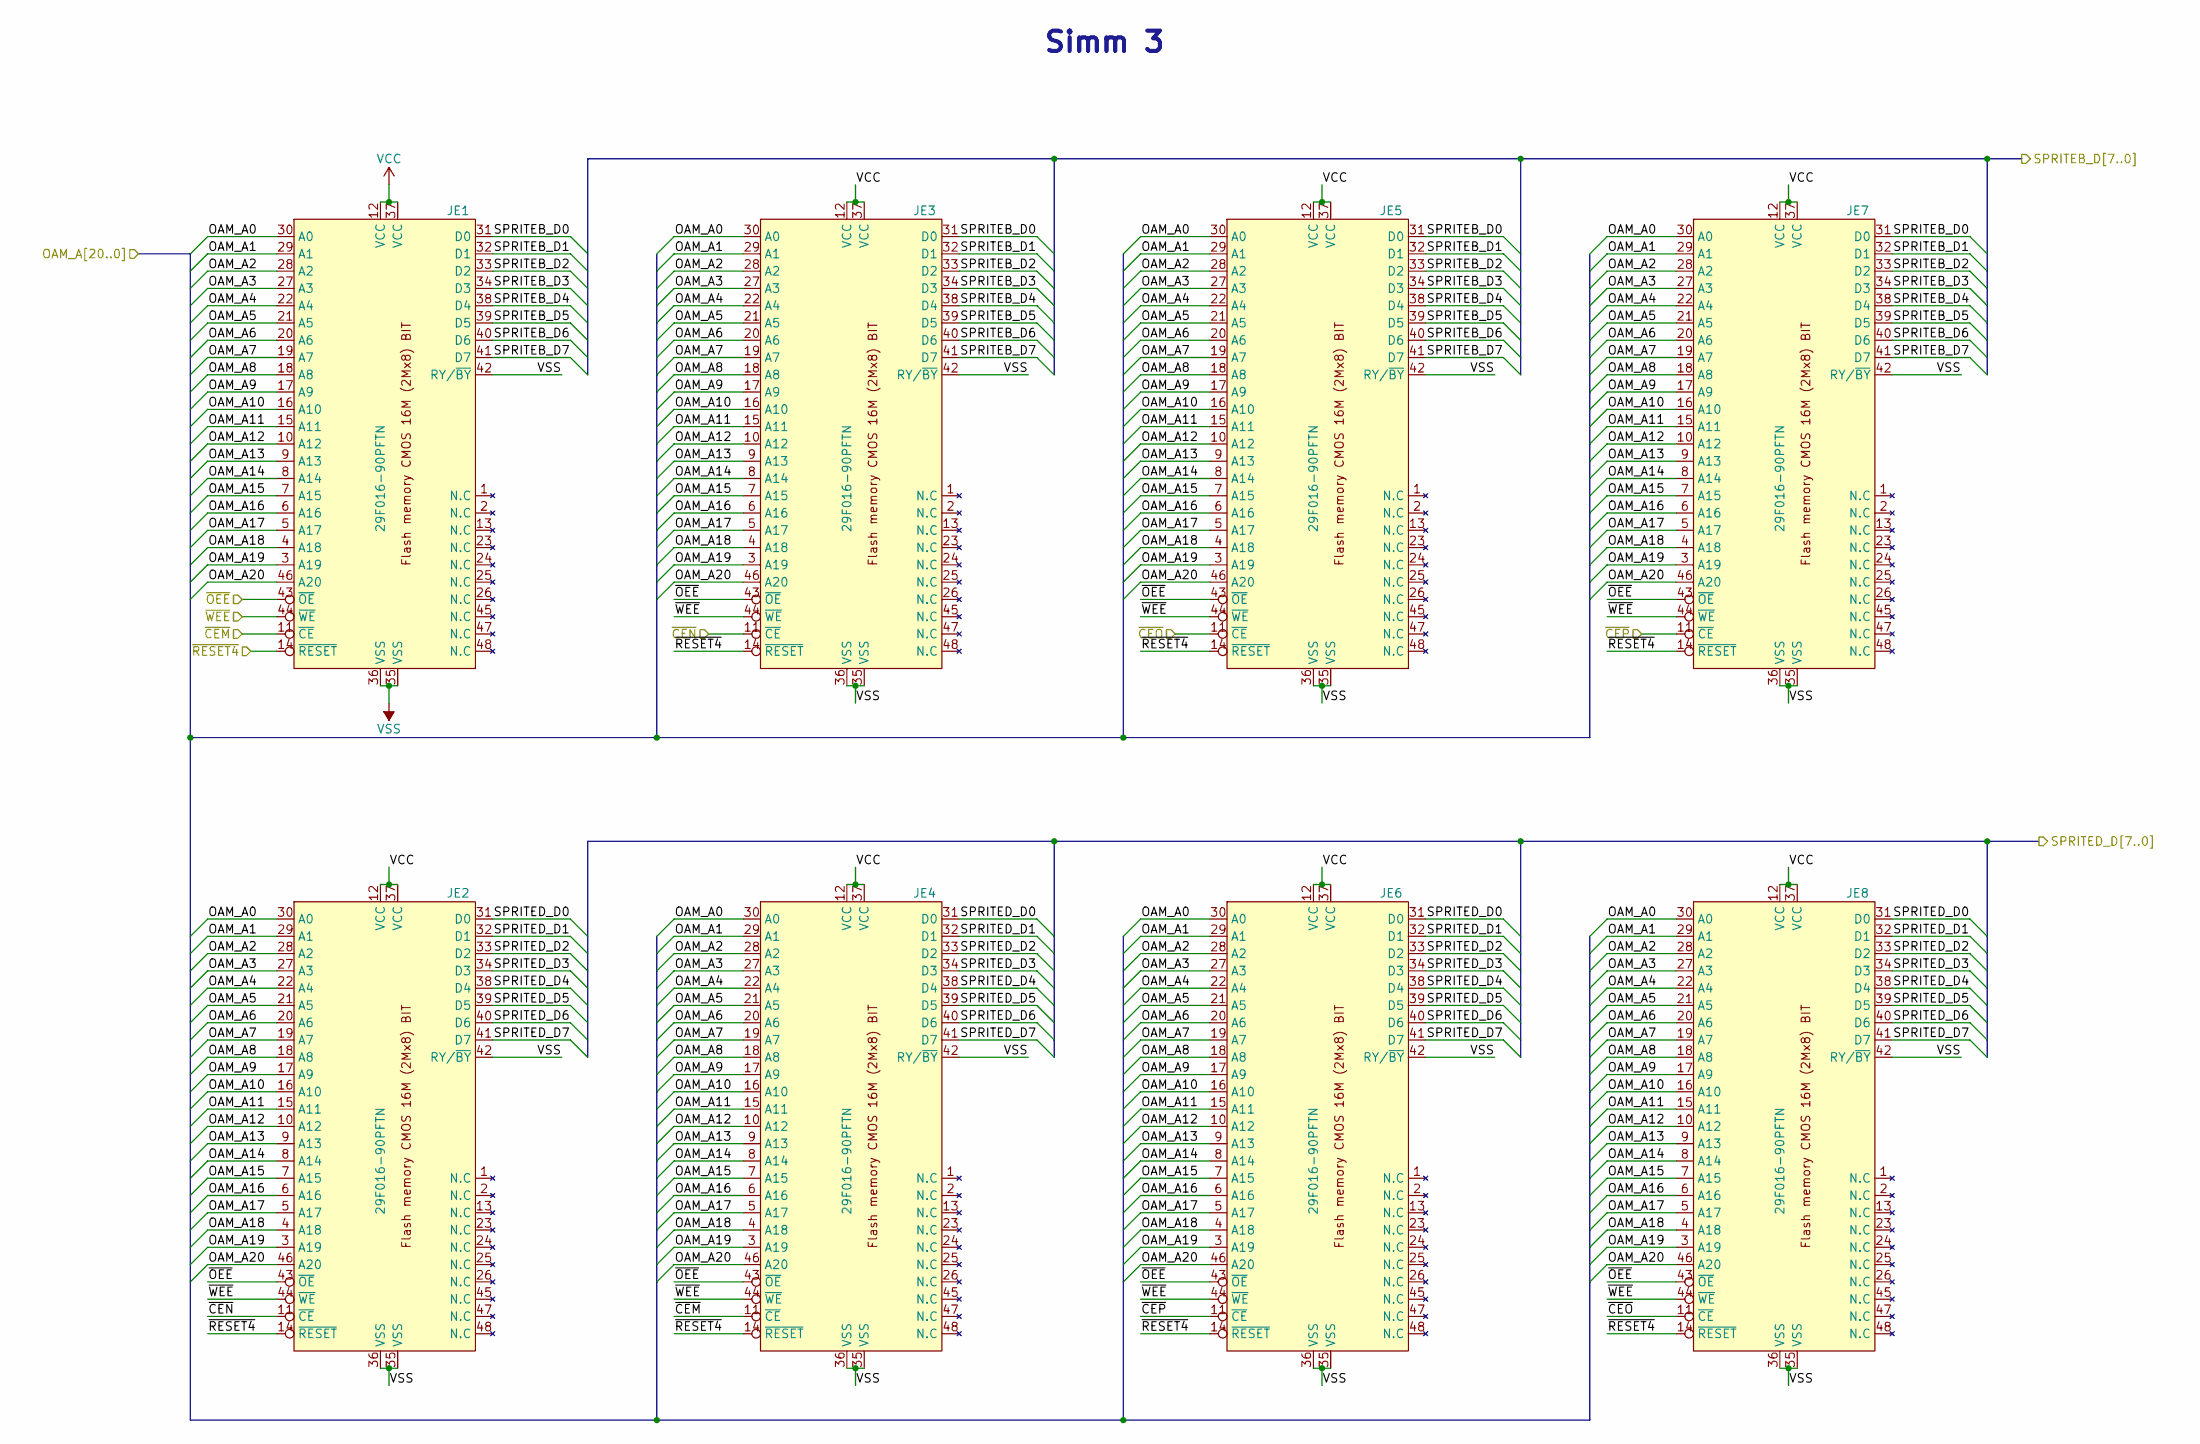
[picture p25: schematic simm3.kicad_sch]

Parts:
JE1, JE2, JE3, JE4, JE5, JE6, JE7, JE8: 29F016-90PFTN

Connections:
unnamed: JE1.12 (VCC), JE1.37 (VCC)
unnamed: JE1.35 (VSS), JE1.36 (VSS)
OAM_A0: JE1.30 (A0), JE2.30 (A0), JE3.30 (A0), JE4.30 (A0), JE5.30 (A0), JE6.30 (A0), JE7.30 (A0), JE8.30 (A0)
OAM_A1: JE1.29 (A1), JE2.29 (A1), JE3.29 (A1), JE4.29 (A1), JE5.29 (A1), JE6.29 (A1), JE7.29 (A1), JE8.29 (A1)
OAM_A2: JE1.28 (A2), JE2.28 (A2), JE3.28 (A2), JE4.28 (A2), JE5.28 (A2), JE6.28 (A2), JE7.28 (A2), JE8.28 (A2)
OAM_A3: JE1.27 (A3), JE2.27 (A3), JE3.27 (A3), JE4.27 (A3), JE5.27 (A3), JE6.27 (A3), JE7.27 (A3), JE8.27 (A3)
OAM_A4: JE1.22 (A4), JE2.22 (A4), JE3.22 (A4), JE4.22 (A4), JE5.22 (A4), JE6.22 (A4), JE7.22 (A4), JE8.22 (A4)
OAM_A5: JE1.21 (A5), JE2.21 (A5), JE3.21 (A5), JE4.21 (A5), JE5.21 (A5), JE6.21 (A5), JE7.21 (A5), JE8.21 (A5)
OAM_A6: JE1.20 (A6), JE2.20 (A6), JE3.20 (A6), JE4.20 (A6), JE5.20 (A6), JE6.20 (A6), JE7.20 (A6), JE8.20 (A6)
OAM_A7: JE1.19 (A7), JE2.19 (A7), JE3.19 (A7), JE4.19 (A7), JE5.19 (A7), JE6.19 (A7), JE7.19 (A7), JE8.19 (A7)
OAM_A8: JE1.18 (A8), JE2.18 (A8), JE3.18 (A8), JE4.18 (A8), JE5.18 (A8), JE6.18 (A8), JE7.18 (A8), JE8.18 (A8)
OAM_A9: JE1.17 (A9), JE2.17 (A9), JE3.17 (A9), JE4.17 (A9), JE5.17 (A9), JE6.17 (A9), JE7.17 (A9), JE8.17 (A9)
OAM_A10: JE1.16 (A10), JE2.16 (A10), JE3.16 (A10), JE4.16 (A10), JE5.16 (A10), JE6.16 (A10), JE7.16 (A10), JE8.16 (A10)
OAM_A11: JE1.15 (A11), JE2.15 (A11), JE3.15 (A11), JE4.15 (A11), JE5.15 (A11), JE6.15 (A11), JE7.15 (A11), JE8.15 (A11)
OAM_A12: JE1.10 (A12), JE2.10 (A12), JE3.10 (A12), JE4.10 (A12), JE5.10 (A12), JE6.10 (A12), JE7.10 (A12), JE8.10 (A12)
OAM_A13: JE1.9 (A13), JE2.9 (A13), JE3.9 (A13), JE4.9 (A13), JE5.9 (A13), JE6.9 (A13), JE7.9 (A13), JE8.9 (A13)
OAM_A14: JE1.8 (A14), JE2.8 (A14), JE3.8 (A14), JE4.8 (A14), JE5.8 (A14), JE6.8 (A14), JE7.8 (A14), JE8.8 (A14)
OAM_A15: JE1.7 (A15), JE2.7 (A15), JE3.7 (A15), JE4.7 (A15), JE5.7 (A15), JE6.7 (A15), JE7.7 (A15), JE8.7 (A15)
OAM_A16: JE1.6 (A16), JE2.6 (A16), JE3.6 (A16), JE4.6 (A16), JE5.6 (A16), JE6.6 (A16), JE7.6 (A16), JE8.6 (A16)
OAM_A17: JE1.5 (A17), JE2.5 (A17), JE3.5 (A17), JE4.5 (A17), JE5.5 (A17), JE6.5 (A17), JE7.5 (A17), JE8.5 (A17)
OAM_A18: JE1.4 (A18), JE2.4 (A18), JE3.4 (A18), JE4.4 (A18), JE5.4 (A18), JE6.4 (A18), JE7.4 (A18), JE8.4 (A18)
OAM_A19: JE1.3 (A19), JE2.3 (A19), JE3.3 (A19), JE4.3 (A19), JE5.3 (A19), JE6.3 (A19), JE7.3 (A19), JE8.3 (A19)
OAM_A20: JE1.46 (A20), JE2.46 (A20), JE3.46 (A20), JE4.46 (A20), JE5.46 (A20), JE6.46 (A20), JE7.46 (A20), JE8.46 (A20)
SPRITEB_D0: JE1.31 (D0), JE3.31 (D0), JE5.31 (D0), JE7.31 (D0)
SPRITEB_D1: JE1.32 (D1), JE3.32 (D1), JE5.32 (D1), JE7.32 (D1)
SPRITEB_D2: JE1.33 (D2), JE3.33 (D2), JE5.33 (D2), JE7.33 (D2)
SPRITEB_D3: JE1.34 (D3), JE3.34 (D3), JE5.34 (D3), JE7.34 (D3)
SPRITEB_D4: JE1.38 (D4), JE3.38 (D4), JE5.38 (D4), JE7.38 (D4)
SPRITEB_D5: JE1.39 (D5), JE3.39 (D5), JE5.39 (D5), JE7.39 (D5)
SPRITEB_D6: JE1.40 (D6), JE3.40 (D6), JE5.40 (D6), JE7.40 (D6)
SPRITEB_D7: JE1.41 (D7), JE3.41 (D7), JE5.41 (D7), JE7.41 (D7)
SPRITED_D0: JE2.31 (D0), JE4.31 (D0), JE6.31 (D0), JE8.31 (D0)
SPRITED_D1: JE2.32 (D1), JE4.32 (D1), JE6.32 (D1), JE8.32 (D1)
SPRITED_D2: JE2.33 (D2), JE4.33 (D2), JE6.33 (D2), JE8.33 (D2)
SPRITED_D3: JE2.34 (D3), JE4.34 (D3), JE6.34 (D3), JE8.34 (D3)
SPRITED_D4: JE2.38 (D4), JE4.38 (D4), JE6.38 (D4), JE8.38 (D4)
SPRITED_D5: JE2.39 (D5), JE4.39 (D5), JE6.39 (D5), JE8.39 (D5)
SPRITED_D6: JE2.40 (D6), JE4.40 (D6), JE6.40 (D6), JE8.40 (D6)
SPRITED_D7: JE2.41 (D7), JE4.41 (D7), JE6.41 (D7), JE8.41 (D7)
VCC: JE2.12 (VCC), JE2.37 (VCC), JE3.12 (VCC), JE3.37 (VCC), JE4.12 (VCC), JE4.37 (VCC), JE5.12 (VCC), JE5.37 (VCC), JE6.12 (VCC), JE6.37 (VCC), JE7.12 (VCC), JE7.37 (VCC), JE8.12 (VCC), JE8.37 (VCC)
VSS: JE1.42 (RY/~BY), JE2.35 (VSS), JE2.36 (VSS), JE2.42 (RY/~BY), JE3.35 (VSS), JE3.36 (VSS), JE3.42 (RY/~BY), JE4.35 (VSS), JE4.36 (VSS), JE4.42 (RY/~BY), JE5.35 (VSS), JE5.36 (VSS), JE5.42 (RY/~BY), JE6.35 (VSS), JE6.36 (VSS), JE6.42 (RY/~BY), JE7.35 (VSS), JE7.36 (VSS), JE7.42 (RY/~BY), JE8.35 (VSS), JE8.36 (VSS), JE8.42 (RY/~BY)
~CEM: JE1.11 (~CE), JE4.11 (~CE)
~CEN: JE2.11 (~CE), JE3.11 (~CE)
~CEO: JE5.11 (~CE), JE8.11 (~CE)
~CEP: JE6.11 (~CE), JE7.11 (~CE)
~OEE: JE1.43 (~OE), JE2.43 (~OE), JE3.43 (~OE), JE4.43 (~OE), JE5.43 (~OE), JE6.43 (~OE), JE7.43 (~OE), JE8.43 (~OE)
~RESET4: JE1.14 (~RESET), JE2.14 (~RESET), JE3.14 (~RESET), JE4.14 (~RESET), JE5.14 (~RESET), JE6.14 (~RESET), JE7.14 (~RESET), JE8.14 (~RESET)
~WEE: JE1.44 (~WE), JE2.44 (~WE), JE3.44 (~WE), JE4.44 (~WE), JE5.44 (~WE), JE6.44 (~WE), JE7.44 (~WE), JE8.44 (~WE)

Notes on the sheet:
Simm 3
