brucejcooper/light_controller/kicad/programmer/programmer.kicad_pcb

## KiCad design cores/cps3/sch/slots_sch.kicad_sch

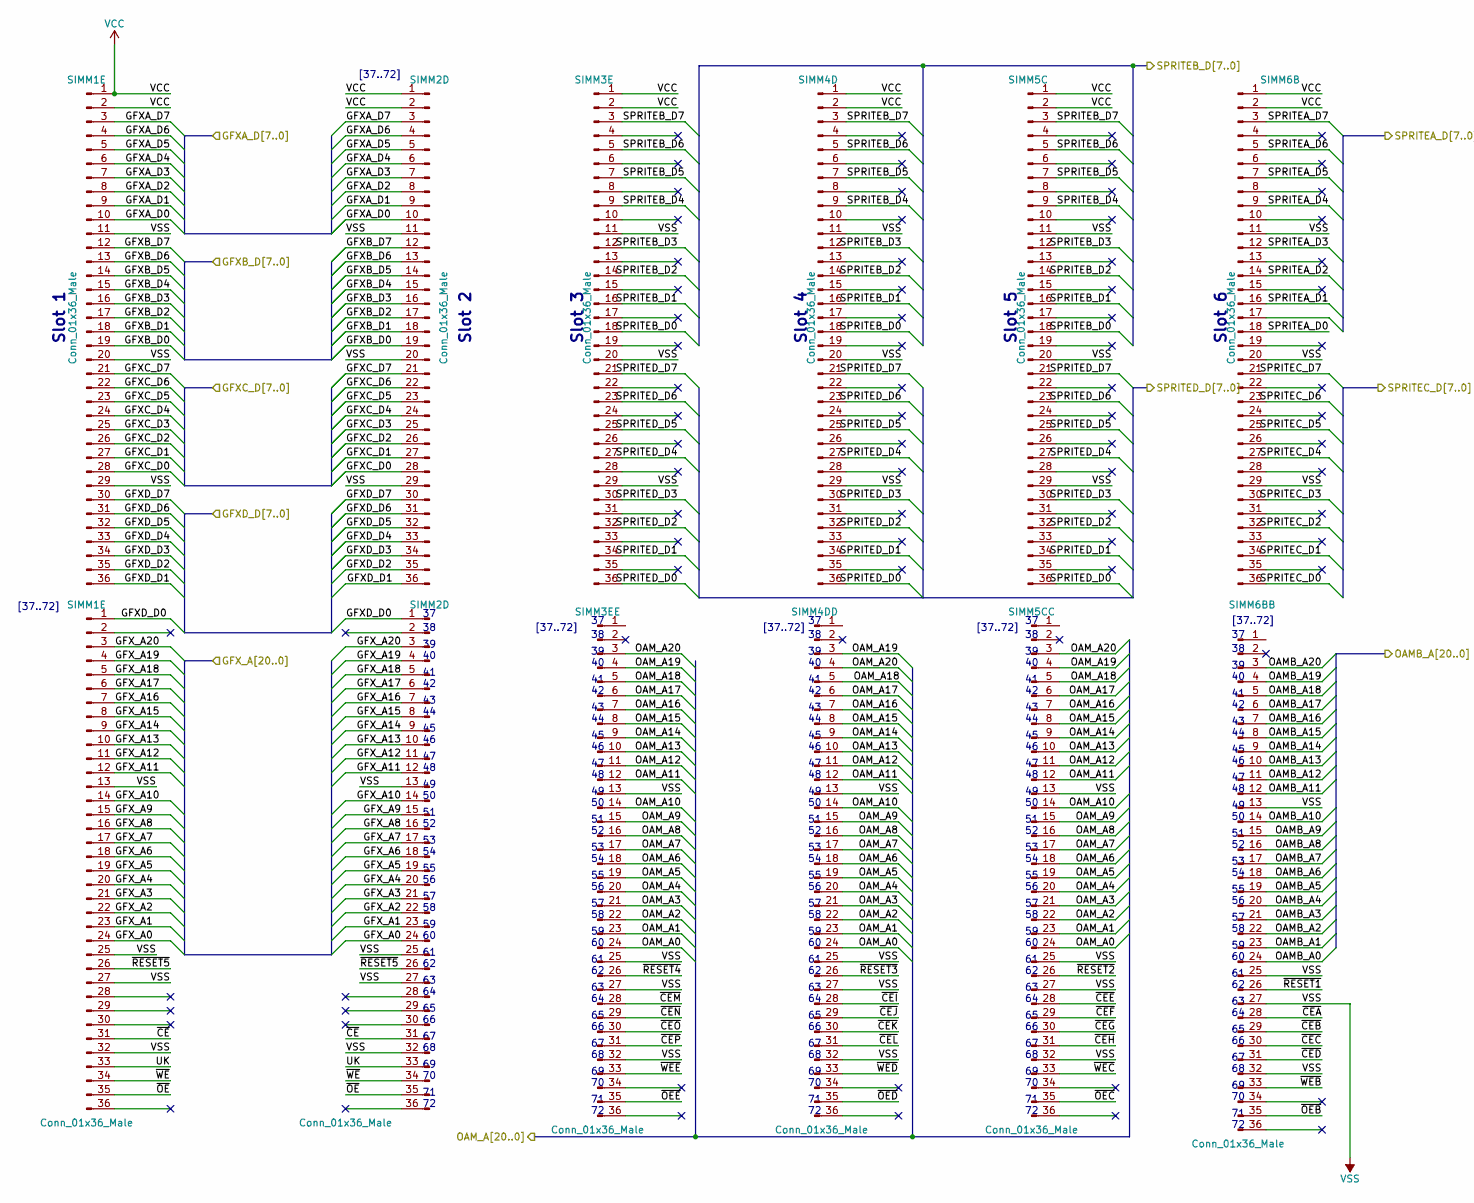
[picture p30: schematic slots_sch.kicad_sch, part in row 1, column 1]

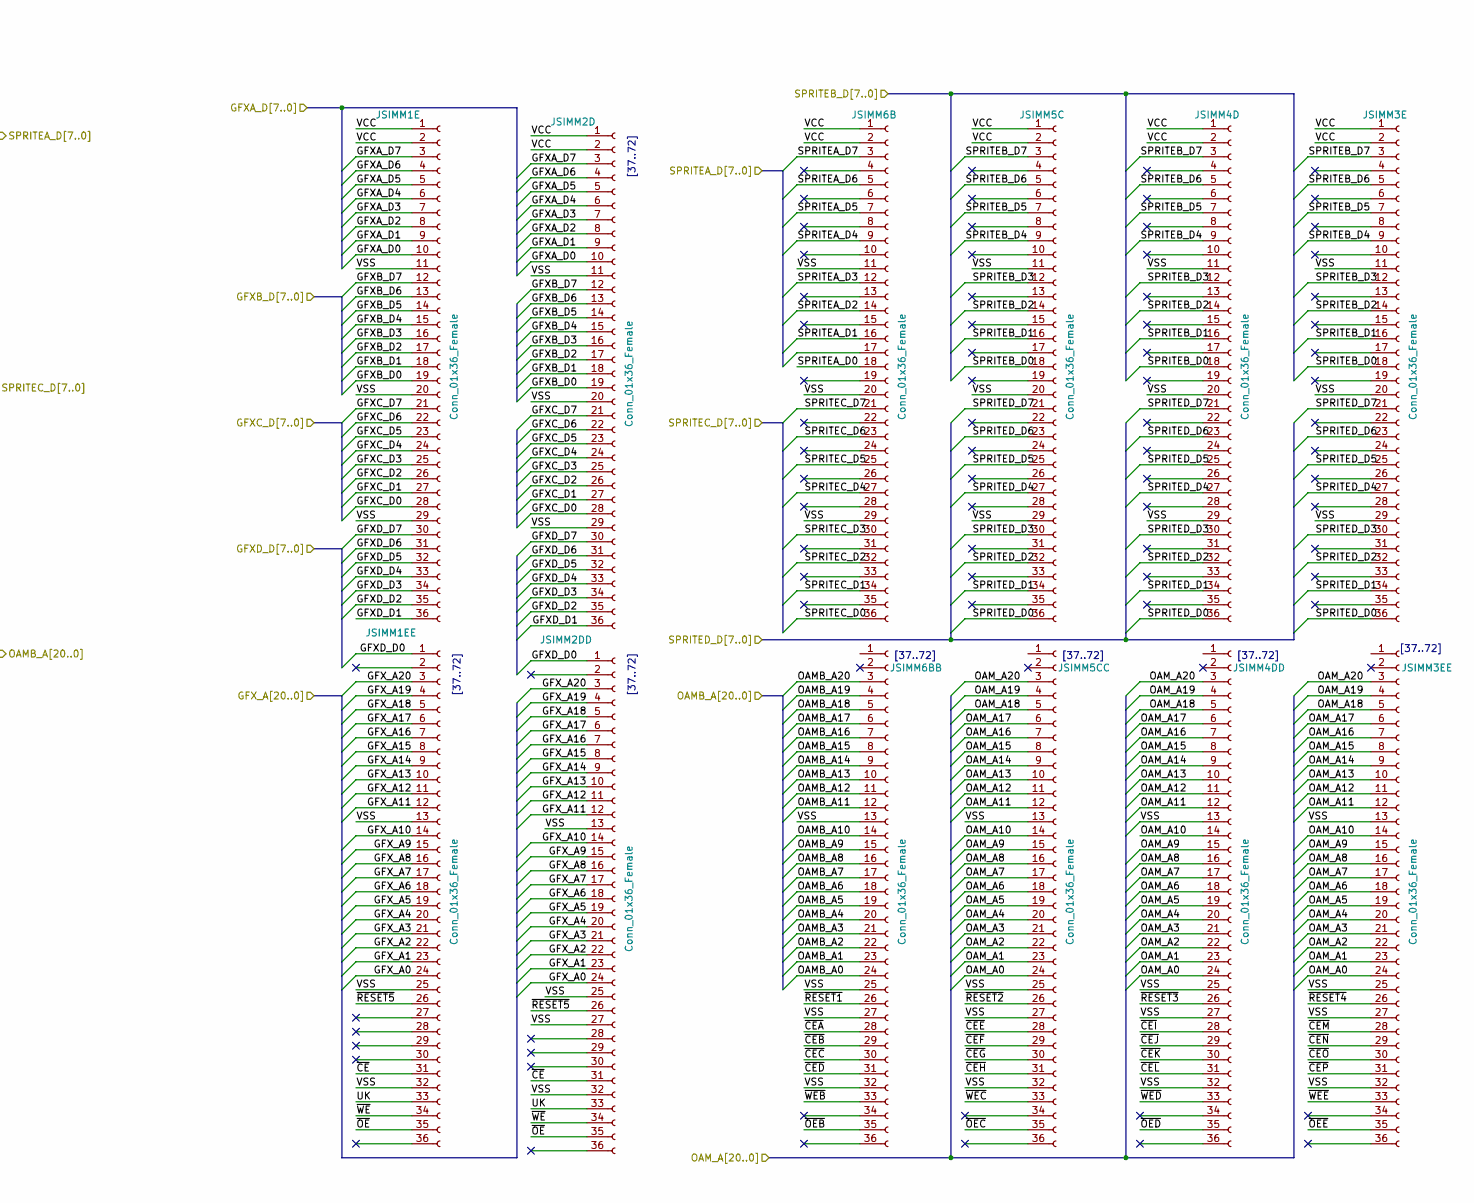
[picture p31: schematic slots_sch.kicad_sch, part in row 1, column 2]

Parts:
JSIMM1E, JSIMM1EE, JSIMM2D, JSIMM2DD, JSIMM3E, JSIMM3EE, JSIMM4D, JSIMM4DD, JSIMM5C, JSIMM5CC, JSIMM6B, JSIMM6BB: Conn_01x36_Female
SIMM1E, SIMM2D, SIMM3E, SIMM3EE, SIMM4D, SIMM4DD, SIMM5C, SIMM5CC, SIMM6B, SIMM6BB: Conn_01x36_Male

Connections:
GFXA_D0: JSIMM1E.10, JSIMM2D.10, SIMM1E.10, SIMM2D.10
GFXA_D1: JSIMM1E.9, JSIMM2D.9, SIMM1E.9, SIMM2D.9
GFXA_D2: JSIMM1E.8, JSIMM2D.8, SIMM1E.8, SIMM2D.8
GFXA_D3: JSIMM1E.7, JSIMM2D.7, SIMM1E.7, SIMM2D.7
GFXA_D4: JSIMM1E.6, JSIMM2D.6, SIMM1E.6, SIMM2D.6
GFXA_D5: JSIMM1E.5, JSIMM2D.5, SIMM1E.5, SIMM2D.5
GFXA_D6: JSIMM1E.4, JSIMM2D.4, SIMM1E.4, SIMM2D.4
GFXA_D7: JSIMM1E.3, JSIMM2D.3, SIMM1E.3, SIMM2D.3
GFXB_D0: JSIMM1E.19, JSIMM2D.19, SIMM1E.19, SIMM2D.19
GFXB_D1: JSIMM1E.18, JSIMM2D.18, SIMM1E.18, SIMM2D.18
GFXB_D2: JSIMM1E.17, JSIMM2D.17, SIMM1E.17, SIMM2D.17
GFXB_D3: JSIMM1E.16, JSIMM2D.16, SIMM1E.16, SIMM2D.16
GFXB_D4: JSIMM1E.15, JSIMM2D.15, SIMM1E.15, SIMM2D.15
GFXB_D5: JSIMM1E.14, JSIMM2D.14, SIMM1E.14, SIMM2D.14
GFXB_D6: JSIMM1E.13, JSIMM2D.13, SIMM1E.13, SIMM2D.13
GFXB_D7: JSIMM1E.12, JSIMM2D.12, SIMM1E.12, SIMM2D.12
GFXC_D0: JSIMM1E.28, JSIMM2D.28, SIMM1E.28, SIMM2D.28
GFXC_D1: JSIMM1E.27, JSIMM2D.27, SIMM1E.27, SIMM2D.27
GFXC_D2: JSIMM1E.26, JSIMM2D.26, SIMM1E.26, SIMM2D.26
GFXC_D3: JSIMM1E.25, JSIMM2D.25, SIMM1E.25, SIMM2D.25
GFXC_D4: JSIMM1E.24, JSIMM2D.24, SIMM1E.24, SIMM2D.24
GFXC_D5: JSIMM1E.23, JSIMM2D.23, SIMM1E.23, SIMM2D.23
GFXC_D6: JSIMM1E.22, JSIMM2D.22, SIMM1E.22, SIMM2D.22
GFXC_D7: JSIMM1E.21, JSIMM2D.21, SIMM1E.21, SIMM2D.21
GFXD_D0: JSIMM1EE.1, JSIMM2DD.1, SIMM1E.1, SIMM2D.1
GFXD_D1: JSIMM1E.36, JSIMM2D.36, SIMM1E.36, SIMM2D.36
GFXD_D2: JSIMM1E.35, JSIMM2D.35, SIMM1E.35, SIMM2D.35
GFXD_D3: JSIMM1E.34, JSIMM2D.34, SIMM1E.34, SIMM2D.34
GFXD_D4: JSIMM1E.33, JSIMM2D.33, SIMM1E.33, SIMM2D.33
GFXD_D5: JSIMM1E.32, JSIMM2D.32, SIMM1E.32, SIMM2D.32
GFXD_D6: JSIMM1E.31, JSIMM2D.31, SIMM1E.31, SIMM2D.31
GFXD_D7: JSIMM1E.30, JSIMM2D.30, SIMM1E.30, SIMM2D.30
GFX_A0: JSIMM1EE.24, JSIMM2DD.24, SIMM1E.24, SIMM2D.24
GFX_A1: JSIMM1EE.23, JSIMM2DD.23, SIMM1E.23, SIMM2D.23
GFX_A2: JSIMM1EE.22, JSIMM2DD.22, SIMM1E.22, SIMM2D.22
GFX_A3: JSIMM1EE.21, JSIMM2DD.21, SIMM1E.21, SIMM2D.21
GFX_A4: JSIMM1EE.20, JSIMM2DD.20, SIMM1E.20, SIMM2D.20
GFX_A5: JSIMM1EE.19, JSIMM2DD.19, SIMM1E.19, SIMM2D.19
GFX_A6: JSIMM1EE.18, JSIMM2DD.18, SIMM1E.18, SIMM2D.18
GFX_A7: JSIMM1EE.17, JSIMM2DD.17, SIMM1E.17, SIMM2D.17
GFX_A8: JSIMM1EE.16, JSIMM2DD.16, SIMM1E.16, SIMM2D.16
GFX_A9: JSIMM1EE.15, JSIMM2DD.15, SIMM1E.15, SIMM2D.15
GFX_A10: JSIMM1EE.14, JSIMM2DD.14, SIMM1E.14, SIMM2D.14
GFX_A11: JSIMM1EE.12, JSIMM2DD.12, SIMM1E.12, SIMM2D.12
GFX_A12: JSIMM1EE.11, JSIMM2DD.11, SIMM1E.11, SIMM2D.11
GFX_A13: JSIMM1EE.10, JSIMM2DD.10, SIMM1E.10, SIMM2D.10
GFX_A14: JSIMM1EE.9, JSIMM2DD.9, SIMM1E.9, SIMM2D.9
GFX_A15: JSIMM1EE.8, JSIMM2DD.8, SIMM1E.8, SIMM2D.8
GFX_A16: JSIMM1EE.7, JSIMM2DD.7, SIMM1E.7, SIMM2D.7
GFX_A17: JSIMM1EE.6, JSIMM2DD.6, SIMM1E.6, SIMM2D.6
GFX_A18: JSIMM1EE.5, JSIMM2DD.5, SIMM1E.5, SIMM2D.5
GFX_A19: JSIMM1EE.4, JSIMM2DD.4, SIMM1E.4, SIMM2D.4
GFX_A20: JSIMM1EE.3, JSIMM2DD.3, SIMM1E.3, SIMM2D.3
OAMB_A0: JSIMM6BB.24, SIMM6BB.24
OAMB_A1: JSIMM6BB.23, SIMM6BB.23
OAMB_A2: JSIMM6BB.22, SIMM6BB.22
OAMB_A3: JSIMM6BB.21, SIMM6BB.21
OAMB_A4: JSIMM6BB.20, SIMM6BB.20
OAMB_A5: JSIMM6BB.19, SIMM6BB.19
OAMB_A6: JSIMM6BB.18, SIMM6BB.18
OAMB_A7: JSIMM6BB.17, SIMM6BB.17
OAMB_A8: JSIMM6BB.16, SIMM6BB.16
OAMB_A9: JSIMM6BB.15, SIMM6BB.15
OAMB_A10: JSIMM6BB.14, SIMM6BB.14
OAMB_A11: JSIMM6BB.12, SIMM6BB.12
OAMB_A12: JSIMM6BB.11, SIMM6BB.11
OAMB_A13: JSIMM6BB.10, SIMM6BB.10
OAMB_A14: JSIMM6BB.9, SIMM6BB.9
OAMB_A15: JSIMM6BB.8, SIMM6BB.8
OAMB_A16: JSIMM6BB.7, SIMM6BB.7
OAMB_A17: JSIMM6BB.6, SIMM6BB.6
OAMB_A18: JSIMM6BB.5, SIMM6BB.5
OAMB_A19: JSIMM6BB.4, SIMM6BB.4
OAMB_A20: JSIMM6BB.3, SIMM6BB.3
OAM_A0: JSIMM3EE.24, JSIMM4DD.24, JSIMM5CC.24, SIMM3EE.24, SIMM4DD.24, SIMM5CC.24
OAM_A1: JSIMM3EE.23, JSIMM4DD.23, JSIMM5CC.23, SIMM3EE.23, SIMM4DD.23, SIMM5CC.23
OAM_A2: JSIMM3EE.22, JSIMM4DD.22, JSIMM5CC.22, SIMM3EE.22, SIMM4DD.22, SIMM5CC.22
OAM_A3: JSIMM3EE.21, JSIMM4DD.21, JSIMM5CC.21, SIMM3EE.21, SIMM4DD.21, SIMM5CC.21
OAM_A4: JSIMM3EE.20, JSIMM4DD.20, JSIMM5CC.20, SIMM3EE.20, SIMM4DD.20, SIMM5CC.20
OAM_A5: JSIMM3EE.19, JSIMM4DD.19, JSIMM5CC.19, SIMM3EE.19, SIMM4DD.19, SIMM5CC.19
OAM_A6: JSIMM3EE.18, JSIMM4DD.18, JSIMM5CC.18, SIMM3EE.18, SIMM4DD.18, SIMM5CC.18
OAM_A7: JSIMM3EE.17, JSIMM4DD.17, JSIMM5CC.17, SIMM3EE.17, SIMM4DD.17, SIMM5CC.17
OAM_A8: JSIMM3EE.16, JSIMM4DD.16, JSIMM5CC.16, SIMM3EE.16, SIMM4DD.16, SIMM5CC.16
OAM_A9: JSIMM3EE.15, JSIMM4DD.15, JSIMM5CC.15, SIMM3EE.15, SIMM4DD.15, SIMM5CC.15
OAM_A10: JSIMM3EE.14, JSIMM4DD.14, JSIMM5CC.14, SIMM3EE.14, SIMM4DD.14, SIMM5CC.14
OAM_A11: JSIMM3EE.12, JSIMM4DD.12, JSIMM5CC.12, SIMM3EE.12, SIMM4DD.12, SIMM5CC.12
OAM_A12: JSIMM3EE.11, JSIMM4DD.11, JSIMM5CC.11, SIMM3EE.11, SIMM4DD.11, SIMM5CC.11
OAM_A13: JSIMM3EE.10, JSIMM4DD.10, JSIMM5CC.10, SIMM3EE.10, SIMM4DD.10, SIMM5CC.10
OAM_A14: JSIMM3EE.9, JSIMM4DD.9, JSIMM5CC.9, SIMM3EE.9, SIMM4DD.9, SIMM5CC.9
OAM_A15: JSIMM3EE.8, JSIMM4DD.8, JSIMM5CC.8, SIMM3EE.8, SIMM4DD.8, SIMM5CC.8
OAM_A16: JSIMM3EE.7, JSIMM4DD.7, JSIMM5CC.7, SIMM3EE.7, SIMM4DD.7, SIMM5CC.7
OAM_A17: JSIMM3EE.6, JSIMM4DD.6, JSIMM5CC.6, SIMM3EE.6, SIMM4DD.6, SIMM5CC.6
OAM_A18: JSIMM3EE.5, JSIMM4DD.5, JSIMM5CC.5, SIMM3EE.5, SIMM4DD.5, SIMM5CC.5
OAM_A19: JSIMM3EE.4, JSIMM4DD.4, JSIMM5CC.4, SIMM3EE.4, SIMM4DD.3, SIMM5CC.4
OAM_A20: JSIMM3EE.3, JSIMM4DD.3, JSIMM5CC.3, SIMM3EE.3, SIMM4DD.4, SIMM5CC.3
SPRITEA_D0: JSIMM6B.18, SIMM6B.18
SPRITEA_D1: JSIMM6B.16, SIMM6B.16
SPRITEA_D2: JSIMM6B.14, SIMM6B.14
SPRITEA_D3: JSIMM6B.12, SIMM6B.12
SPRITEA_D4: JSIMM6B.9, SIMM6B.9
SPRITEA_D5: JSIMM6B.7, SIMM6B.7
SPRITEA_D6: JSIMM6B.5, SIMM6B.5
SPRITEA_D7: JSIMM6B.3, SIMM6B.3
SPRITEB_D0: JSIMM3E.18, JSIMM4D.18, JSIMM5C.18, SIMM3E.18, SIMM4D.18, SIMM5C.18
SPRITEB_D1: JSIMM3E.16, JSIMM4D.16, JSIMM5C.16, SIMM3E.16, SIMM4D.16, SIMM5C.16
SPRITEB_D2: JSIMM3E.14, JSIMM4D.14, JSIMM5C.14, SIMM3E.14, SIMM4D.14, SIMM5C.14
SPRITEB_D3: JSIMM3E.12, JSIMM4D.12, JSIMM5C.12, SIMM3E.12, SIMM4D.12, SIMM5C.12
SPRITEB_D4: JSIMM3E.9, JSIMM4D.9, JSIMM5C.9, SIMM3E.9, SIMM4D.9, SIMM5C.9
SPRITEB_D5: JSIMM3E.7, JSIMM4D.7, JSIMM5C.7, SIMM3E.7, SIMM4D.7, SIMM5C.7
SPRITEB_D6: JSIMM3E.5, JSIMM4D.5, JSIMM5C.5, SIMM3E.5, SIMM4D.5, SIMM5C.5
SPRITEB_D7: JSIMM3E.3, JSIMM4D.3, JSIMM5C.3, SIMM3E.3, SIMM4D.3, SIMM5C.3
SPRITEC_D0: JSIMM6B.36, SIMM6B.36
SPRITEC_D1: JSIMM6B.34, SIMM6B.34
SPRITEC_D2: JSIMM6B.32, SIMM6B.32
SPRITEC_D3: JSIMM6B.30, SIMM6B.30
SPRITEC_D4: JSIMM6B.27, SIMM6B.27
SPRITEC_D5: JSIMM6B.25, SIMM6B.25
SPRITEC_D6: JSIMM6B.23, SIMM6B.23
SPRITEC_D7: JSIMM6B.21, SIMM6B.21
SPRITED_D0: JSIMM3E.36, JSIMM4D.36, JSIMM5C.36, SIMM3E.36, SIMM4D.36, SIMM5C.36
SPRITED_D1: JSIMM3E.34, JSIMM4D.34, JSIMM5C.34, SIMM3E.34, SIMM4D.34, SIMM5C.34
SPRITED_D2: JSIMM3E.32, JSIMM4D.32, JSIMM5C.32, SIMM3E.32, SIMM4D.32, SIMM5C.32
SPRITED_D3: JSIMM3E.30, JSIMM4D.30, JSIMM5C.30, SIMM3E.30, SIMM4D.30, SIMM5C.30
SPRITED_D4: JSIMM3E.27, JSIMM4D.27, JSIMM5C.27, SIMM3E.27, SIMM4D.27, SIMM5C.27
SPRITED_D5: JSIMM3E.25, JSIMM4D.25, JSIMM5C.25, SIMM3E.25, SIMM4D.25, SIMM5C.25
SPRITED_D6: JSIMM3E.23, JSIMM4D.23, JSIMM5C.23, SIMM3E.23, SIMM4D.23, SIMM5C.23
SPRITED_D7: JSIMM3E.21, JSIMM4D.21, JSIMM5C.21, SIMM3E.21, SIMM4D.21, SIMM5C.21
UK: JSIMM1EE.33, JSIMM2DD.33, SIMM1E.33, SIMM2D.33
VCC: JSIMM1E.1, JSIMM1E.2, JSIMM2D.1, JSIMM2D.2, JSIMM3E.1, JSIMM3E.2, JSIMM4D.1, JSIMM4D.2, JSIMM5C.1, JSIMM5C.2, JSIMM6B.1, JSIMM6B.2, SIMM1E.1, SIMM1E.2, SIMM2D.1, SIMM2D.2, SIMM3E.1, SIMM3E.2, SIMM4D.1, SIMM4D.2, SIMM5C.1, SIMM5C.2, SIMM6B.1, SIMM6B.2
VSS: JSIMM1E.11, JSIMM1E.20, JSIMM1E.29, JSIMM1EE.13, JSIMM1EE.25, JSIMM1EE.32, JSIMM2D.11, JSIMM2D.20, JSIMM2D.29, JSIMM2DD.13, JSIMM2DD.25, JSIMM2DD.27, JSIMM2DD.32, JSIMM3E.11, JSIMM3E.20, JSIMM3E.29, JSIMM3EE.13, JSIMM3EE.25, JSIMM3EE.27, JSIMM3EE.32, JSIMM4D.11, JSIMM4D.20, JSIMM4D.29, JSIMM4DD.13, JSIMM4DD.25, JSIMM4DD.27, JSIMM4DD.32, JSIMM5C.11, JSIMM5C.20, JSIMM5C.29, JSIMM5CC.13, JSIMM5CC.25, JSIMM5CC.27, JSIMM5CC.32, JSIMM6B.11, JSIMM6B.20, JSIMM6B.29, JSIMM6BB.13, JSIMM6BB.25, JSIMM6BB.27, JSIMM6BB.32, SIMM1E.11, SIMM1E.13, SIMM1E.20, SIMM1E.25, SIMM1E.27, SIMM1E.29, SIMM1E.32, SIMM2D.11, SIMM2D.13, SIMM2D.20, SIMM2D.25, SIMM2D.27, SIMM2D.29, SIMM2D.32, SIMM3E.11, SIMM3E.20, SIMM3E.29, SIMM3EE.13, SIMM3EE.25, SIMM3EE.27, SIMM3EE.32, SIMM4D.11, SIMM4D.20, SIMM4D.29, SIMM4DD.13, SIMM4DD.25, SIMM4DD.27, SIMM4DD.32, SIMM5C.11, SIMM5C.20, SIMM5C.29, SIMM5CC.13, SIMM5CC.25, SIMM5CC.27, SIMM5CC.32, SIMM6B.11, SIMM6B.20, SIMM6B.29, SIMM6BB.13, SIMM6BB.25, SIMM6BB.27, SIMM6BB.32
~CEA: JSIMM6BB.28, SIMM6BB.28
~CEB: JSIMM6BB.29, SIMM6BB.29
~CEC: JSIMM6BB.30, SIMM6BB.30
~CED: JSIMM6BB.31, SIMM6BB.31
~CEE: JSIMM5CC.28, SIMM5CC.28
~CEF: JSIMM5CC.29, SIMM5CC.29
~CEG: JSIMM5CC.30, SIMM5CC.30
~CEH: JSIMM5CC.31, SIMM5CC.31
~CEI: JSIMM4DD.28, SIMM4DD.28
~CEJ: JSIMM4DD.29, SIMM4DD.29
~CEK: JSIMM4DD.30, SIMM4DD.30
~CEL: JSIMM4DD.31, SIMM4DD.31
~CEM: JSIMM3EE.28, SIMM3EE.28
~CEN: JSIMM3EE.29, SIMM3EE.29
~CEO: JSIMM3EE.30, SIMM3EE.30
~CEP: JSIMM3EE.31, SIMM3EE.31
~CE: JSIMM1EE.31, JSIMM2DD.31, SIMM1E.31, SIMM2D.31
~OEB: JSIMM6BB.35, SIMM6BB.35
~OEC: JSIMM5CC.35, SIMM5CC.35
~OED: JSIMM4DD.35, SIMM4DD.35
~OEE: JSIMM3EE.35, SIMM3EE.35
~OE: JSIMM1EE.35, JSIMM2DD.35, SIMM1E.35, SIMM2D.35
~RESET1: JSIMM6BB.26, SIMM6BB.26
~RESET2: JSIMM5CC.26, SIMM5CC.26
~RESET3: JSIMM4DD.26, SIMM4DD.26
~RESET4: JSIMM3EE.26, SIMM3EE.26
~RESET5: JSIMM1EE.26, JSIMM2DD.26, SIMM1E.26, SIMM2D.26
~WEB: JSIMM6BB.33, SIMM6BB.33
~WEC: JSIMM5CC.33, SIMM5CC.33
~WED: JSIMM4DD.33, SIMM4DD.33
~WEE: JSIMM3EE.33, SIMM3EE.33
~WE: JSIMM1EE.34, JSIMM2DD.34, SIMM1E.34, SIMM2D.34

Notes on the sheet:
Slot 5
45 46
[37..72]
59 60
67 68
61 62
65 66
47 48
41 42
Slot 3
51 52
71 72
63 64
49 50
69 70
43 44
57 58
39 40
53 54
55 56
Slot 2
Slot 4
Slot 1
Slot 6
