brucejcooper/light_controller/kicad/programmer/programmer.kicad_pcb

## KiCad design cores/cps3/sch/trans.kicad_sch

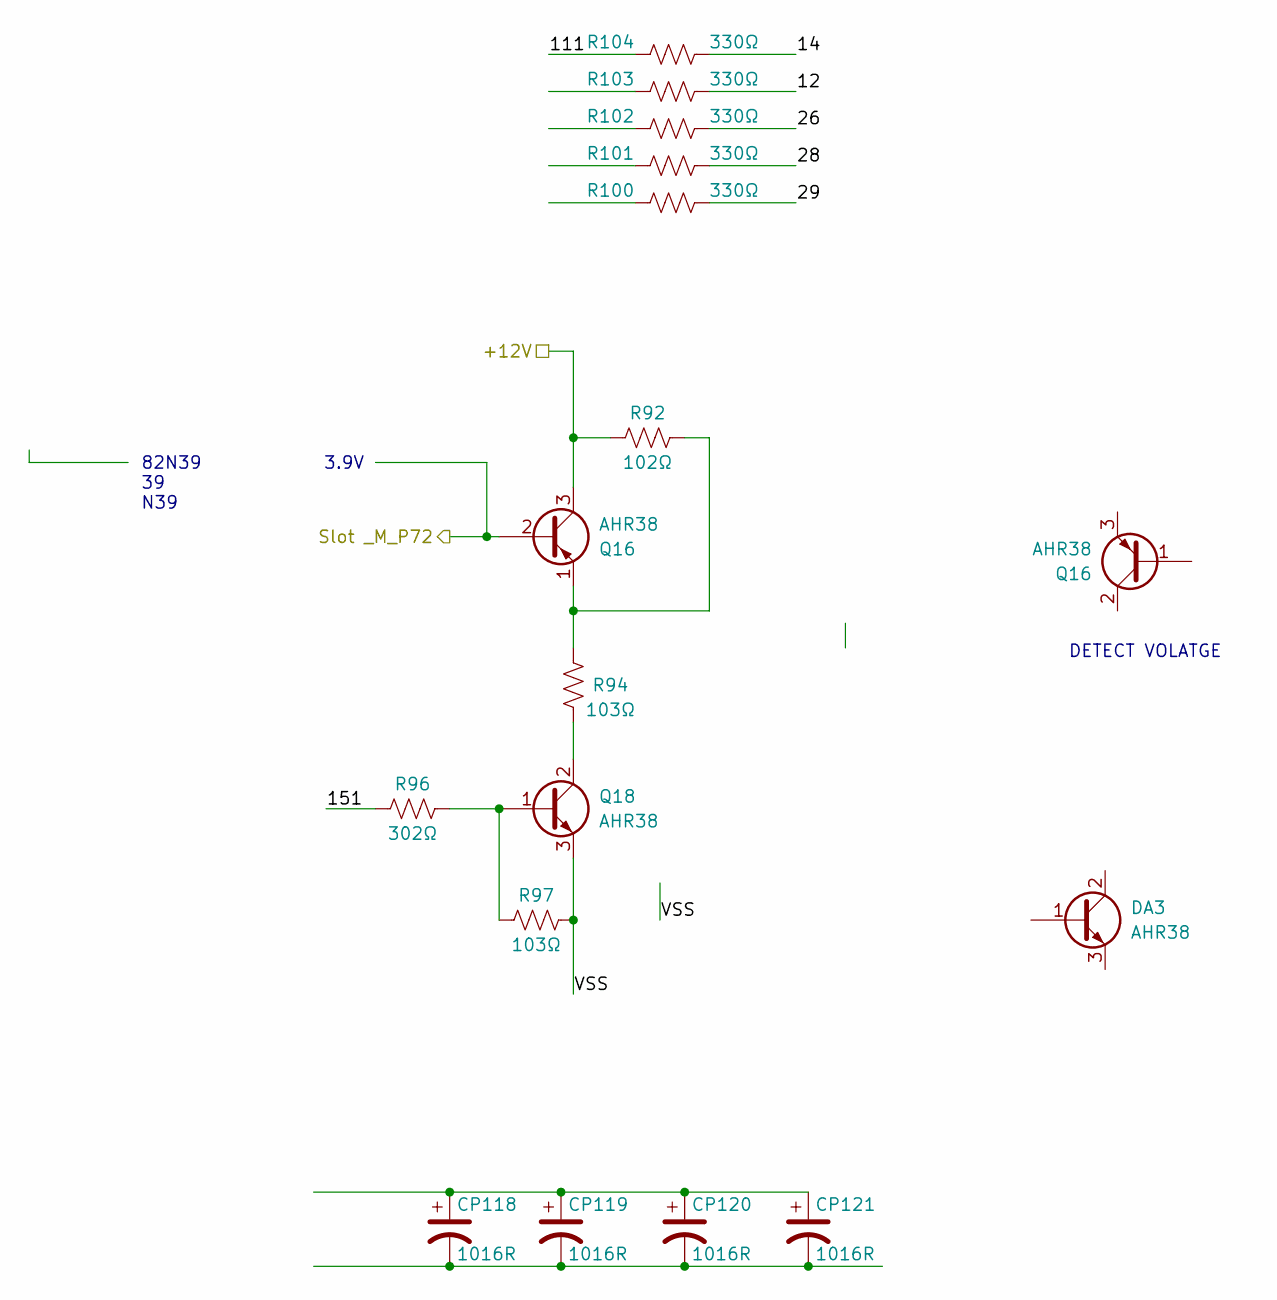
[picture p32: schematic trans.kicad_sch]

Parts:
CP118, CP119, CP120, CP121: 1016R
DA3: AHR38
Q16, Q18: AHR38
R92: 102Ω
R94, R97: 103Ω
R96: 302Ω
R100, R101, R102, R103, R104: 330Ω

Connections:
12: R103.2
14: R104.2
26: R102.2
28: R101.2
29: R100.2
111: R104.1
151: R96.1
+12V: Q16.3 (E), R92.1
unnamed: CP118.1, CP119.1, CP120.1, CP121.1
unnamed: CP118.2, CP119.2, CP120.2, CP121.2
unnamed: Q16.1 (B), R92.2, R94.1
unnamed: Q18.1 (B), R96.2, R97.1
unnamed: Q18.2 (C), R94.2
Slot _M_P72: Q16.2 (C)
VSS: Q18.3 (E), R97.2

Notes on the sheet:
DETECT VOLATGE
82N39 3.9V 39 N39
